Raviolifun/FiveBarRobot/CAD_Model/Electronics/motor-driver-odrive-v3-6-1.snapshot.2/motor driver.png

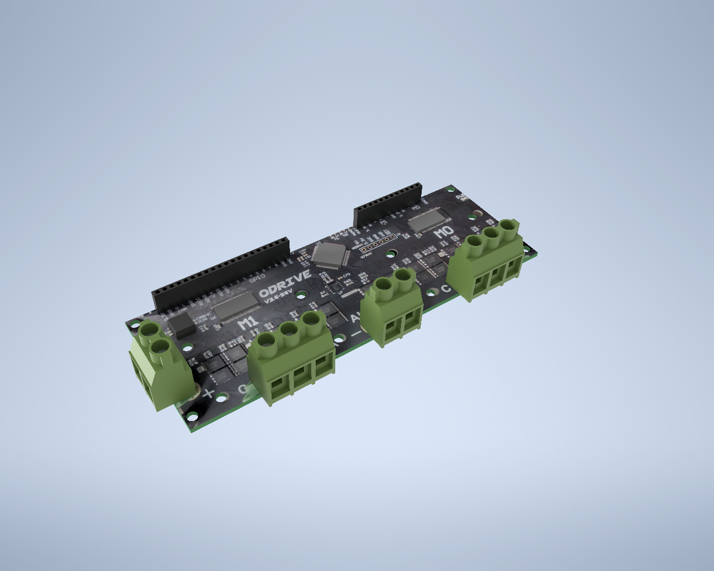
CAD_Model/Electronics/motor-driver-odrive-v3-6-1.snapshot.2/motor driver.png
