Raviolifun/FiveBarRobot/CAD_Model/Electronics/noctua-nf-a8-pwm-fan-80x80x25-1.snapshot.3/1.JPG

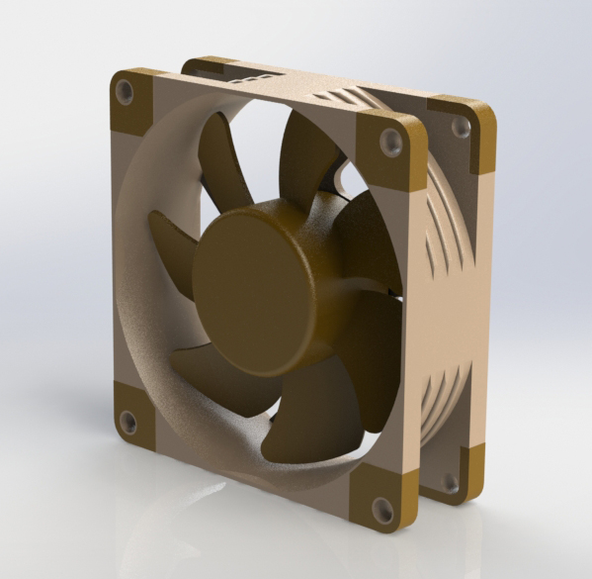
CAD_Model/Electronics/noctua-nf-a8-pwm-fan-80x80x25-1.snapshot.3/1.JPG
