Raviolifun/FiveBarRobot/CAD_Model/Motor/Renders/Motor1.JPG

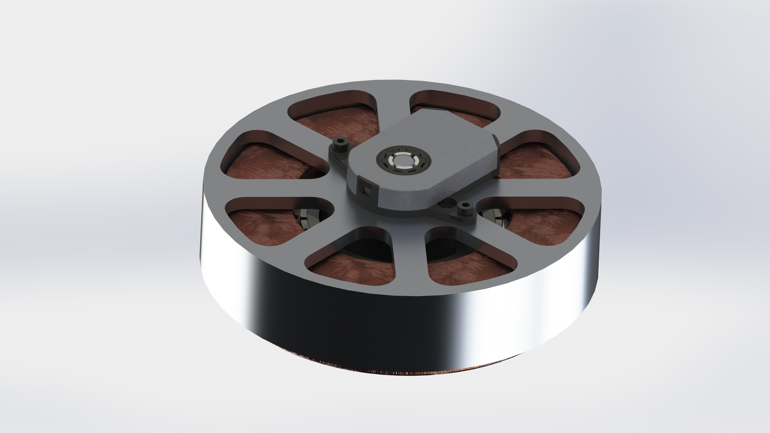
CAD_Model/Motor/Renders/Motor1.JPG
