Raviolifun/FiveBarRobot/CAD_Model/Renders/Robot.JPG

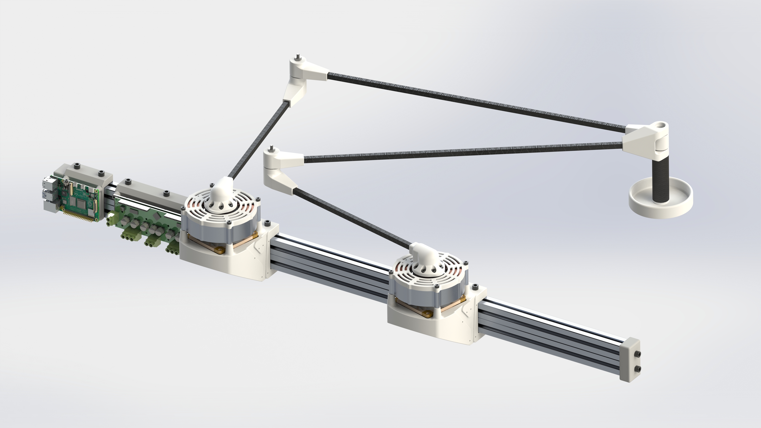
CAD_Model/Renders/Robot.JPG
