Raviolifun/FiveBarRobot/CAD_Model/Renders/Table.JPG

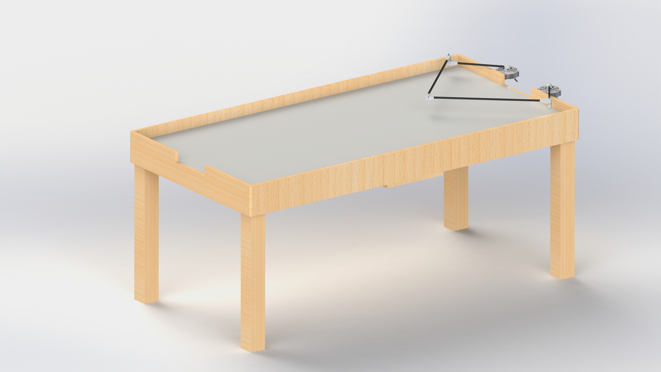
CAD_Model/Renders/Table.JPG
