Raviolifun/FiveBarRobot/CAD_Model/Renders/TableTop.JPG

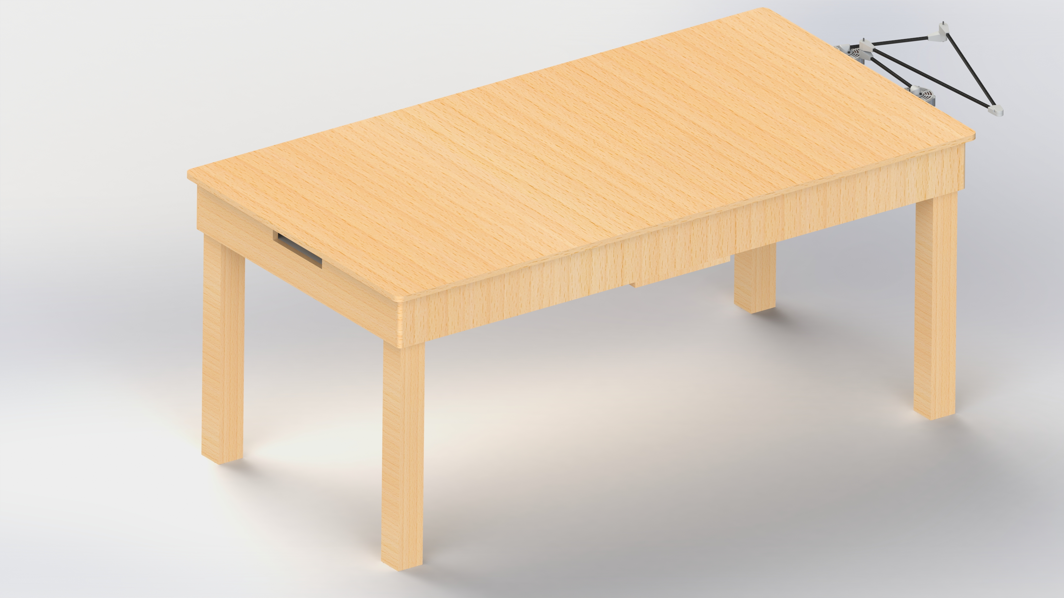
CAD_Model/Renders/TableTop.JPG
