Raviolifun/FiveBarRobot/Saves/animation.gif

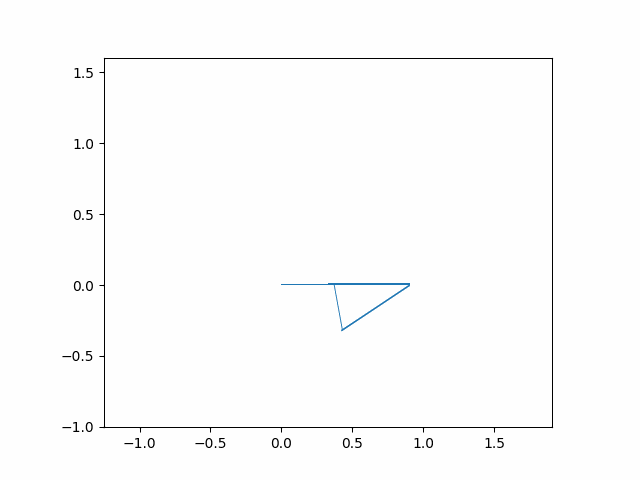
Saves/animation.gif
