Raviolifun/FiveBarRobot/Saves/e3.png

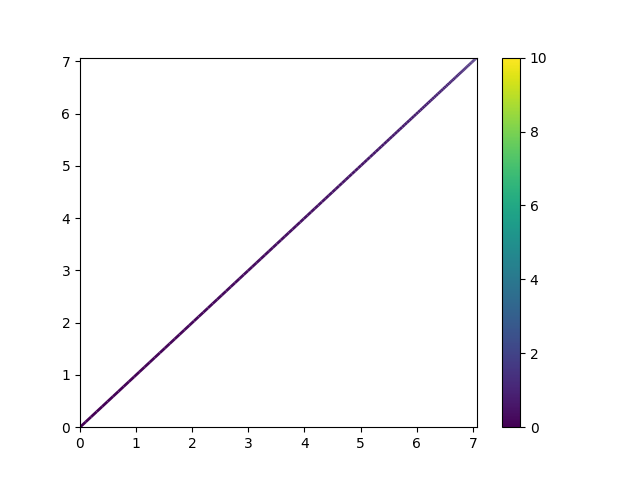
Saves/e3.png
