Raviolifun/FiveBarRobot/Saves/e3_hard.png

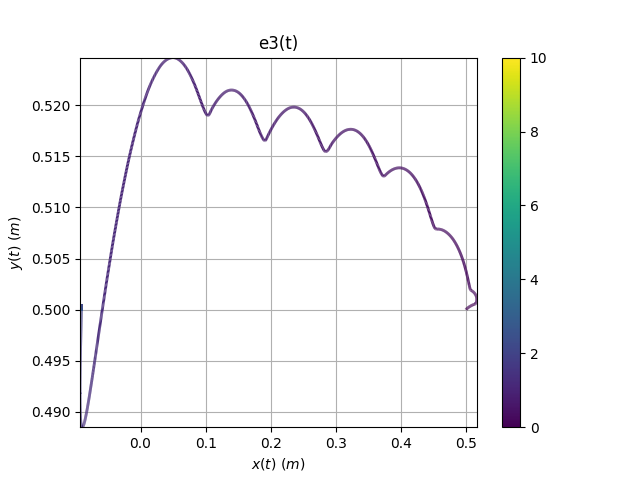
Saves/e3_hard.png
