Raviolifun/FiveBarRobot/Simulator/Saves/e3.png

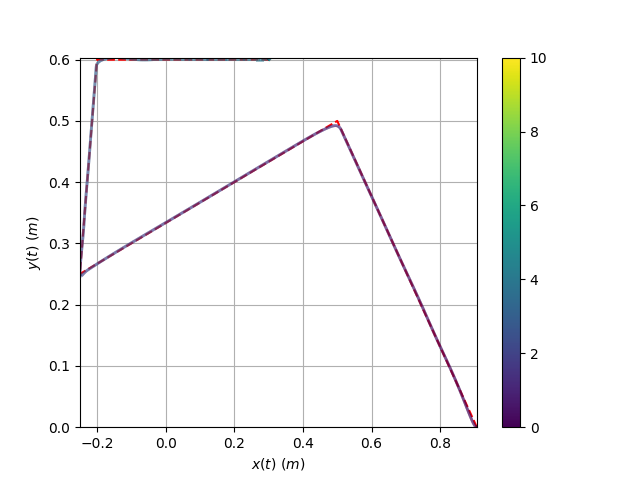
Simulator/Saves/e3.png
