Raviolifun/FiveBarRobot/Simulator/Visualize/Save/VisualizePlayArea.png

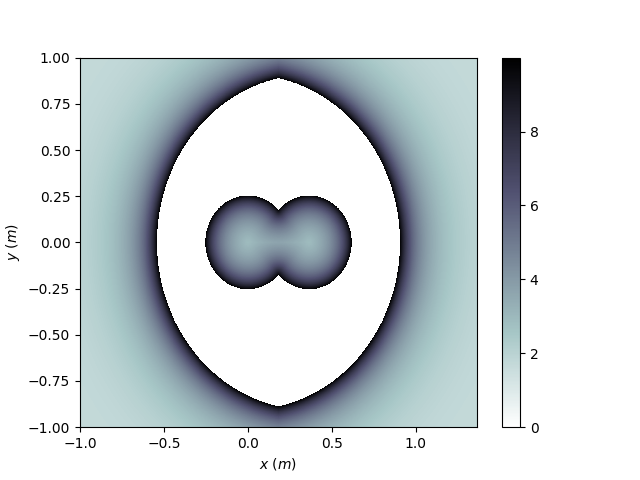
Simulator/Visualize/Save/VisualizePlayArea.png
