Raviolifun/FiveBarRobot/Simulator/Visualize/Save/VisualizePlayAreaDistance.png

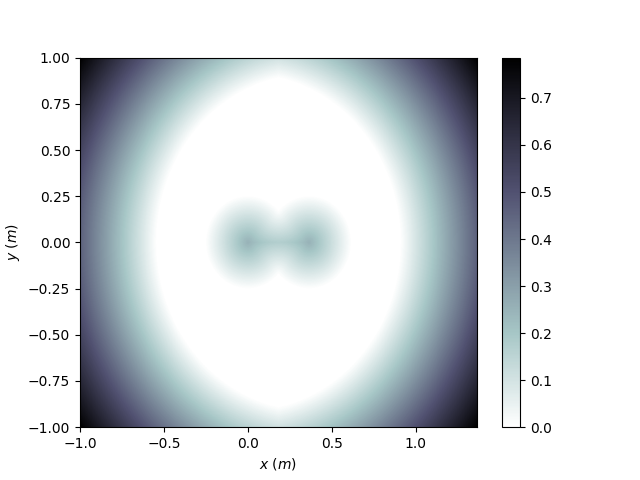
Simulator/Visualize/Save/VisualizePlayAreaDistance.png
