Raviolifun/FiveBarRobot/CAD_Model/Motor/Electronics/cui-devices-atm102-atm103-encoders-1.snapshot.5/FreeCAD Files/Encoders.FCStd

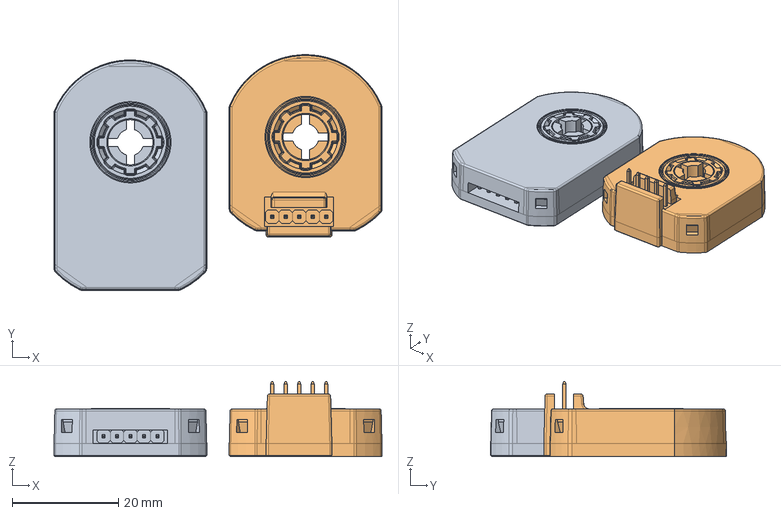
[picture p31: CAD file, 2023-01-07]
CAD_Model/Motor/Electronics/cui-devices-atm102-atm103-encoders-1.snapshot.5/FreeCAD Files/Encoders.FCStd
61.8 x 44.4 x 14.2 mm
ATM102 Encoder_001
ATM103 Encoder_001
