Raviolifun/FiveBarRobot/CAD_Model/Motor/StatorRotor/RI100-210120.stp

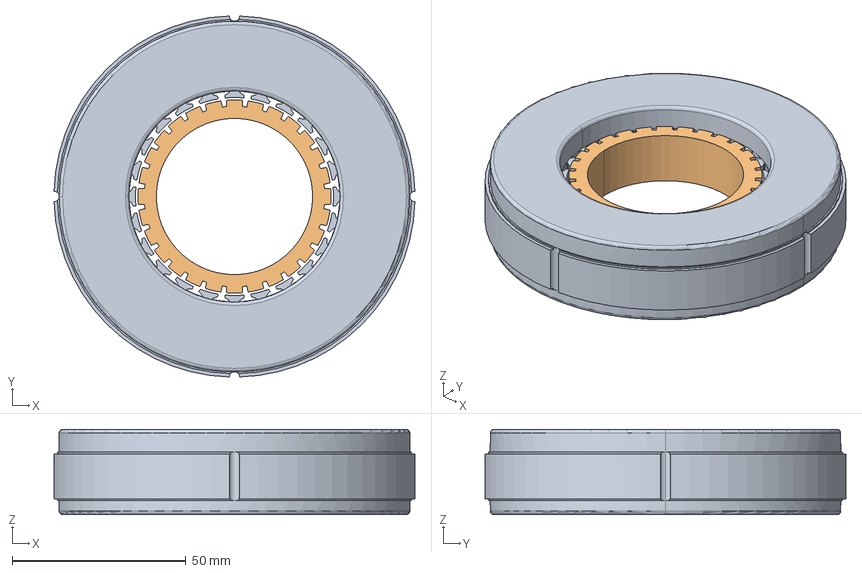
[picture p32: CAD file, 2022-10-18]
CAD_Model/Motor/StatorRotor/RI100-210120.stp
104.0 x 104.0 x 24.5 mm
