Raviolifun/FiveBarRobot/CAD_Model/TestSystem/TestSystem_1.STL

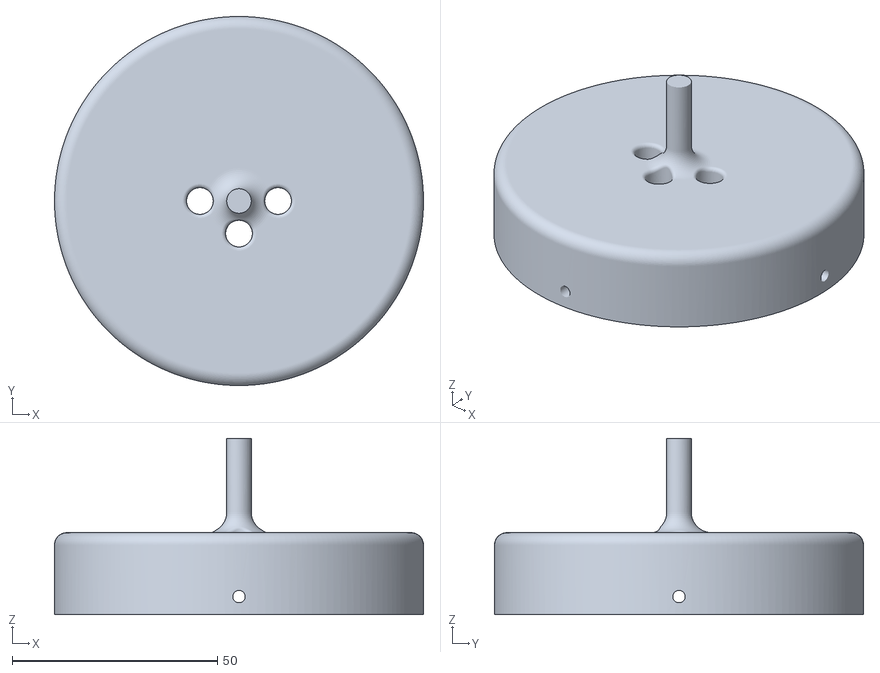
[picture p33: CAD file, 2023-04-11]
CAD_Model/TestSystem/TestSystem_1.STL
90.0 x 90.0 x 43.0
