Raviolifun/FiveBarRobot/CAM_Profiles/2x_StatorWorkHolding.STL

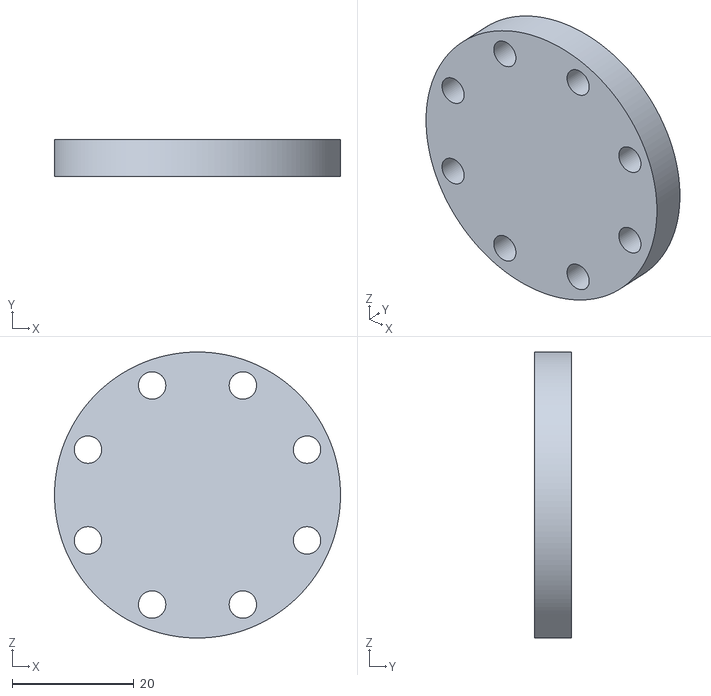
[picture p34: CAD file, 2023-04-11]
CAM_Profiles/2x_StatorWorkHolding.STL
47.0 x 6.00 x 47.0
