Raviolifun/FiveBarRobot/CAD_Model/AirTable/Electronics Mount.SLDPRT

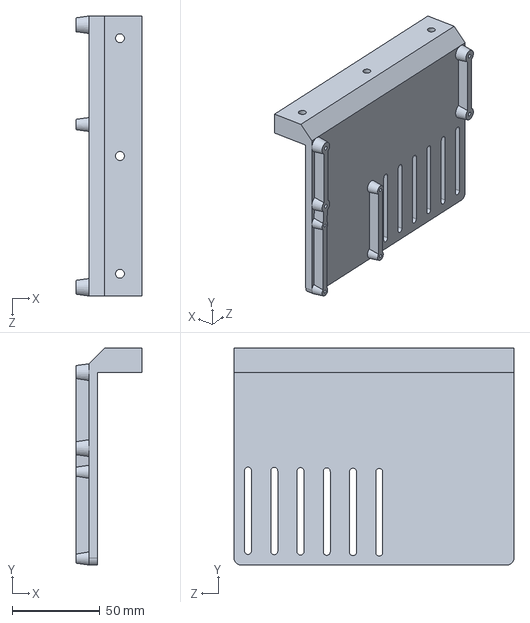
[picture p35: CAD file, 2023-02-09]
CAD_Model/AirTable/Electronics Mount.SLDPRT
37.9 x 124.0 x 160.0 mm
