Raviolifun/FiveBarRobot/CAD_Model/AirTable/SubParts/Leg2.SLDPRT

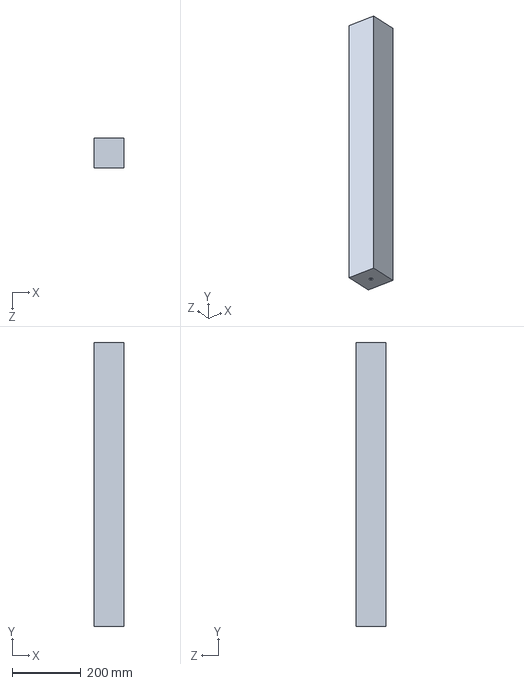
[picture p36: CAD file, 2023-02-06]
CAD_Model/AirTable/SubParts/Leg2.SLDPRT
88.9 x 828.7 x 88.9 mm
