Raviolifun/FiveBarRobot/CAD_Model/Electronics/noctua-nf-a8-pwm-fan-80x80x25-1.snapshot.3/Import_Noctua nf-a8-pwm fan 80x80x25.SLDPRT

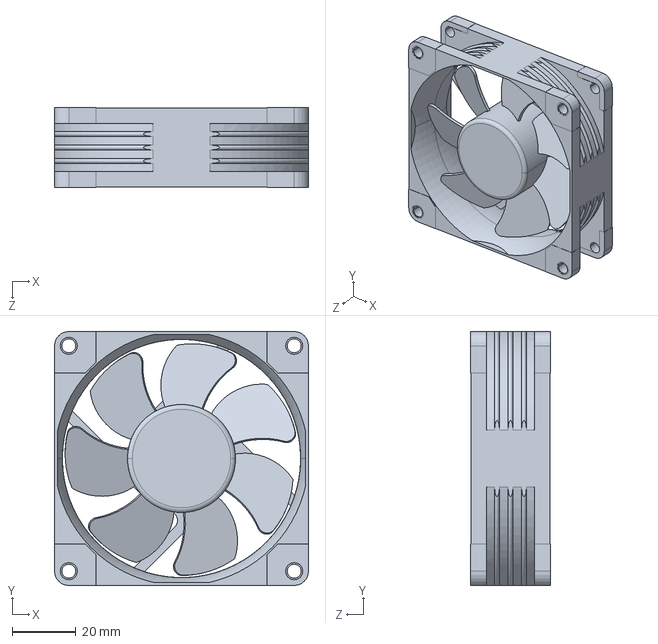
[picture p37: CAD file, 2023-02-09]
CAD_Model/Electronics/noctua-nf-a8-pwm-fan-80x80x25-1.snapshot.3/Import_Noctua nf-a8-pwm fan 80x80x25.SLDPRT
80.0 x 80.0 x 25.2 mm
