Raviolifun/FiveBarRobot/CAD_Model/Electronics/raspberry-pi-4-model-b-1.snapshot.3/2.54 mm DUPONT MALE PIN HEADER, IO, 2X20, RPi4ModelB.SLDPRT

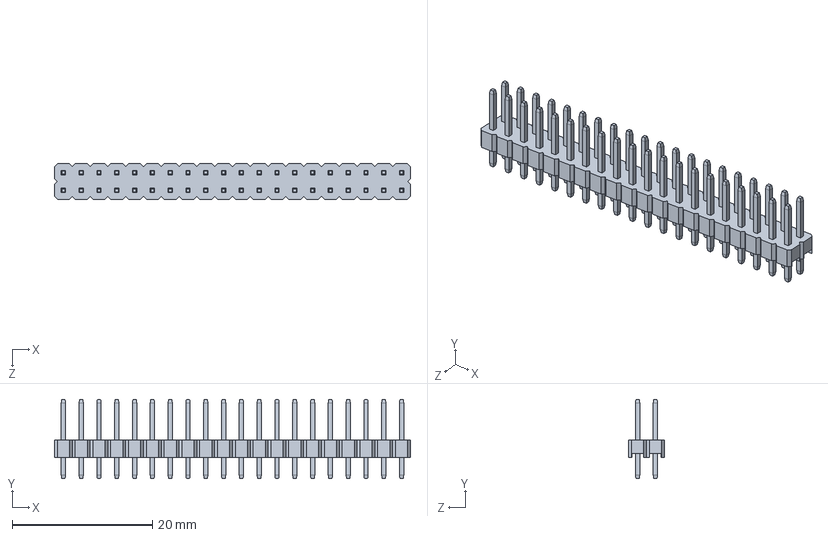
[picture p38: CAD file, 2023-01-13]
CAD_Model/Electronics/raspberry-pi-4-model-b-1.snapshot.3/2.54 mm DUPONT MALE PIN HEADER, IO, 2X20, RPi4ModelB.SLDPRT
50.8 x 11.3 x 5.08 mm
