Raviolifun/FiveBarRobot/CAD_Model/Export3DPrinting/Robot_EndJoint_Spacer.STL

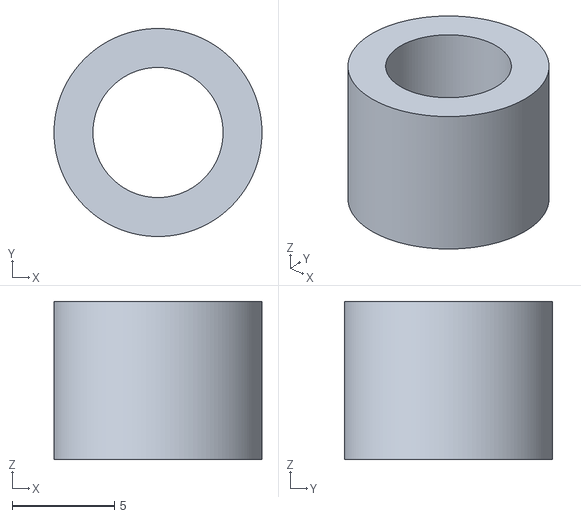
[picture p39: CAD file, 2023-04-05]
CAD_Model/Export3DPrinting/Robot_EndJoint_Spacer.STL
10.2 x 10.2 x 7.72
