Raviolifun/FiveBarRobot/CAD_Model/Export3DPrinting/ToPrint/Aestetic_Edge_Guard.STL

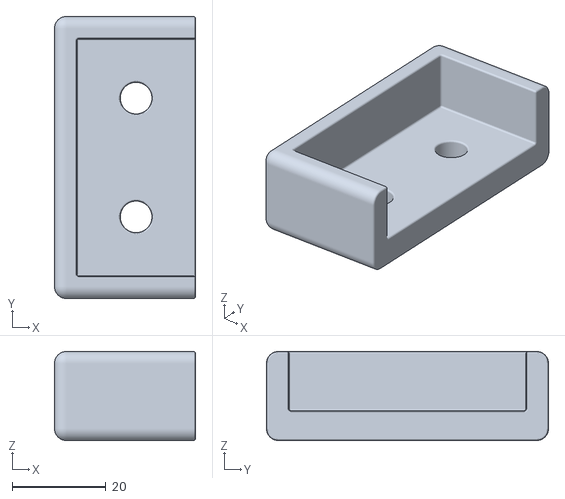
[picture p40: CAD file, 2023-02-09]
CAD_Model/Export3DPrinting/ToPrint/Aestetic_Edge_Guard.STL
30.2 x 60.3 x 19.1
