Raviolifun/FiveBarRobot/CAD_Model/Motor/Electronics/cui-devices-atm102-atm103-encoders-1.snapshot.5/ATM103 Encoder.step

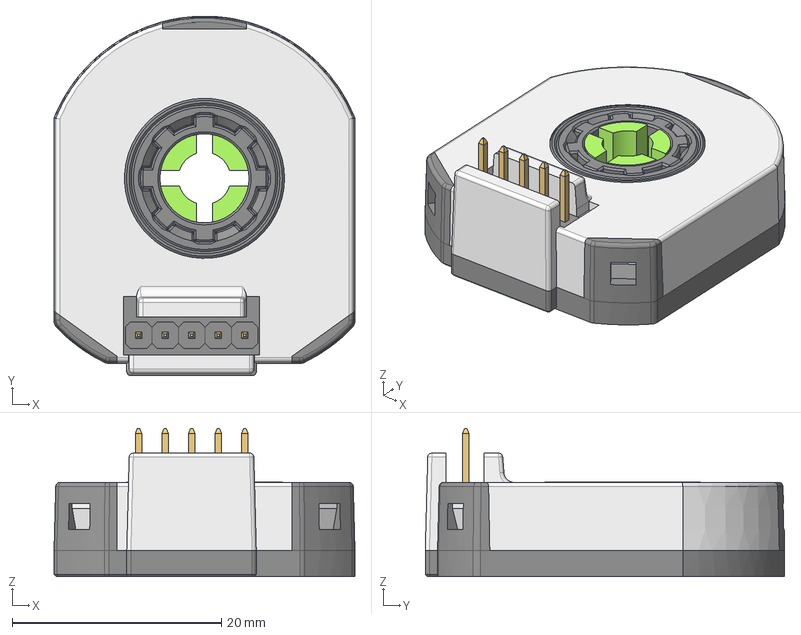
[picture p41: CAD file, 2023-01-07]
CAD_Model/Motor/Electronics/cui-devices-atm102-atm103-encoders-1.snapshot.5/ATM103 Encoder.step
28.8 x 34.4 x 14.2 mm
