Raviolifun/FiveBarRobot/CAD_Model/Motor/Stator.SLDPRT

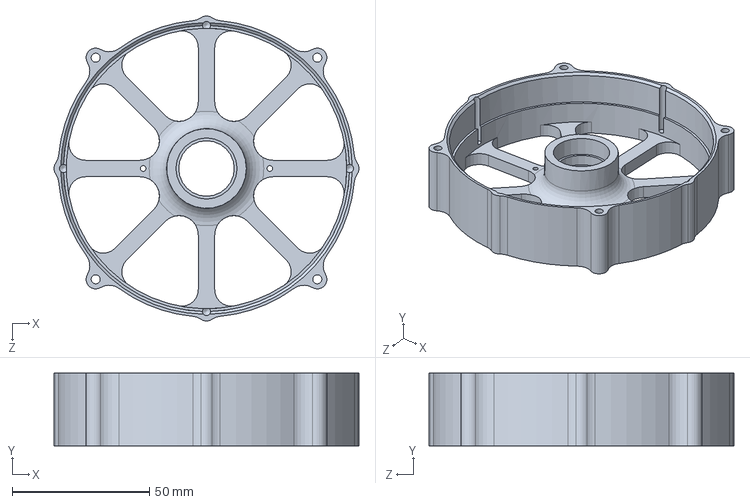
[picture p42: CAD file, 2023-02-06]
CAD_Model/Motor/Stator.SLDPRT
110.9 x 26.5 x 110.9 mm
