Raviolifun/FiveBarRobot/CAD_Model/TestSystem/TestSystem_2.STL

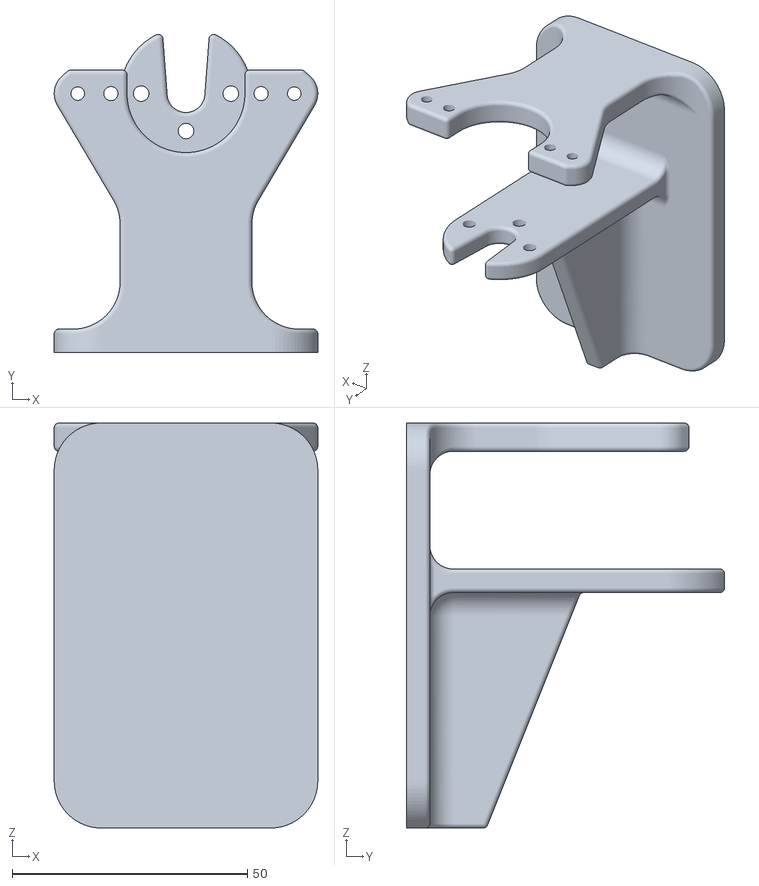
[picture p43: CAD file, 2023-04-11]
CAD_Model/TestSystem/TestSystem_2.STL
56.0 x 67.6 x 86.0
