Raviolifun/FiveBarRobot/CAM_Profiles/StatorWorkHolding.STEP

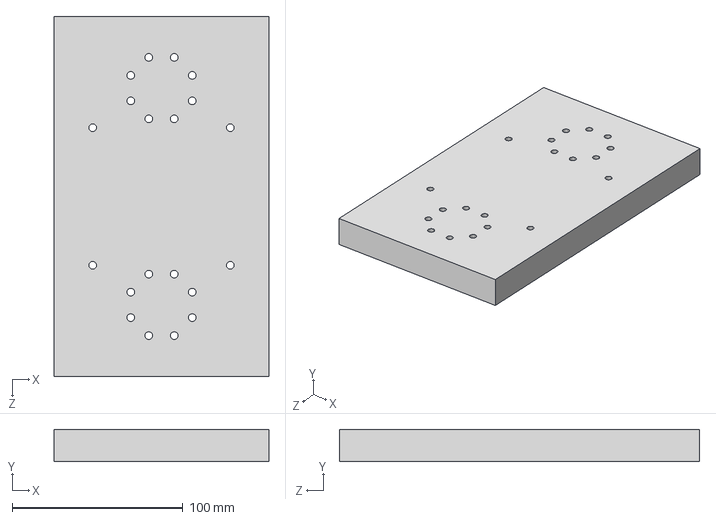
[picture p44: CAD file, 2023-04-11]
CAM_Profiles/StatorWorkHolding.STEP
126.0 x 19.0 x 211.1 mm
