Raviolifun/FiveBarRobot/CAD_Model/AirTable/SubParts/DuctBottom.SLDPRT

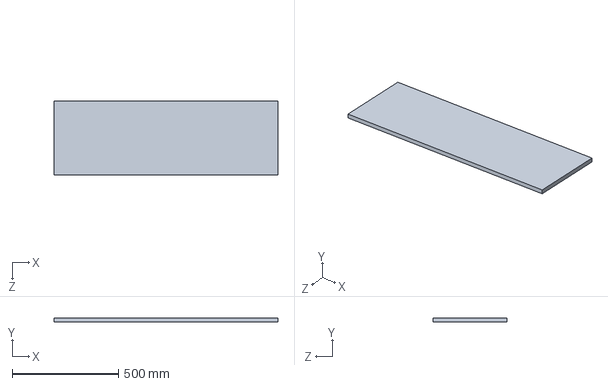
[picture p45: CAD file, 2023-02-06]
CAD_Model/AirTable/SubParts/DuctBottom.SLDPRT
1054.1 x 19.1 x 346.1 mm
