Raviolifun/FiveBarRobot/CAD_Model/Electronics/raspberry-pi-4-model-b-1.snapshot.3/91D77 D9WHV 778K, 4 GB LPDDR4 SDRAM, RPi4ModelB.SLDPRT

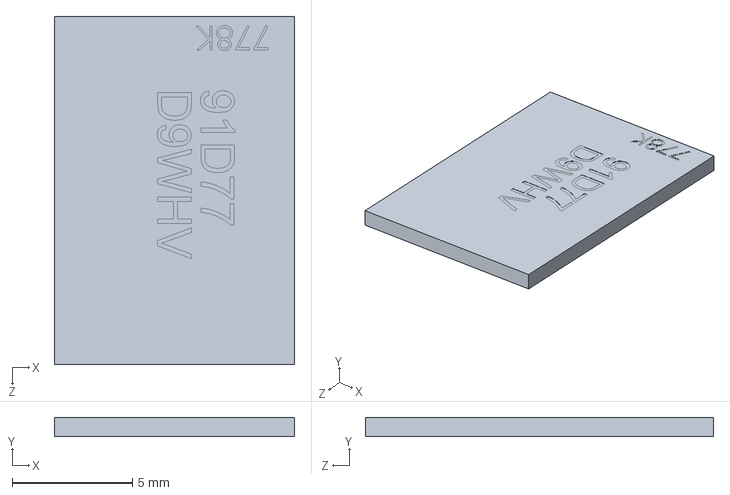
[picture p46: CAD file, 2023-01-13]
CAD_Model/Electronics/raspberry-pi-4-model-b-1.snapshot.3/91D77 D9WHV 778K, 4 GB LPDDR4 SDRAM, RPi4ModelB.SLDPRT
10.0 x 0.8 x 14.5 mm
