Raviolifun/FiveBarRobot/CAD_Model/Motor/Rotor.SLDPRT

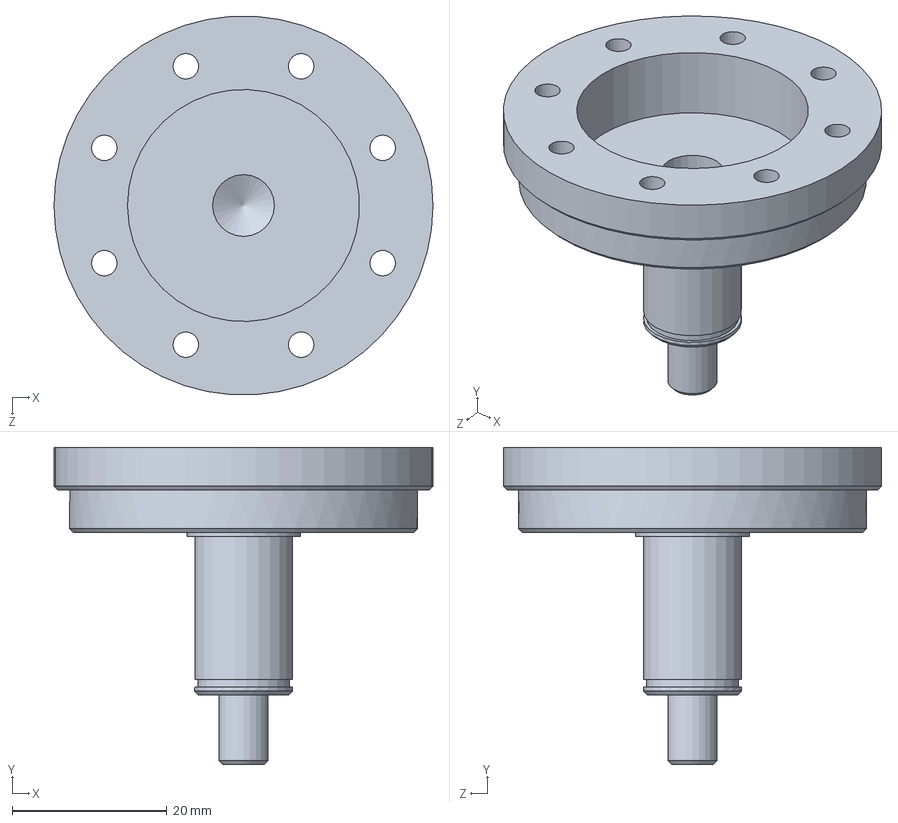
[picture p47: CAD file, 2023-02-06]
CAD_Model/Motor/Rotor.SLDPRT
49.0 x 41.0 x 48.9 mm
