Raviolifun/FiveBarRobot/CAD_Model/TestSystem/TestSystem.SLDPRT

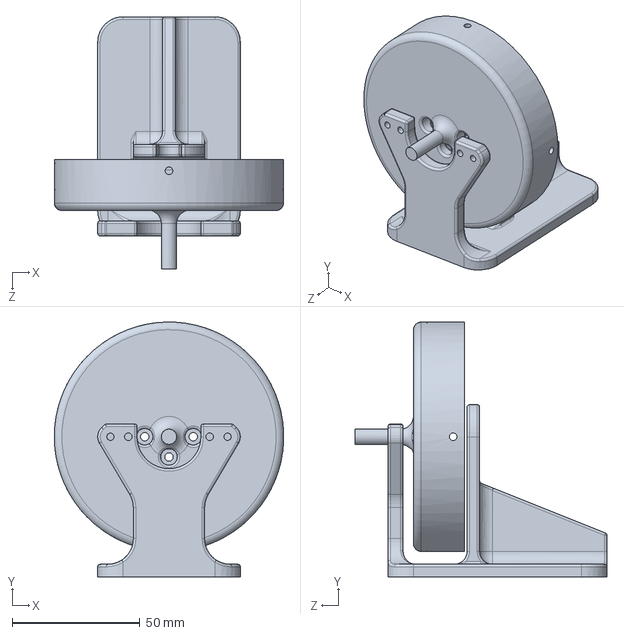
[picture p48: CAD file, 2023-04-11]
CAD_Model/TestSystem/TestSystem.SLDPRT
90.0 x 100.0 x 99.0 mm
