Raviolifun/FiveBarRobot/CAM_Profiles/Rotor.STEP

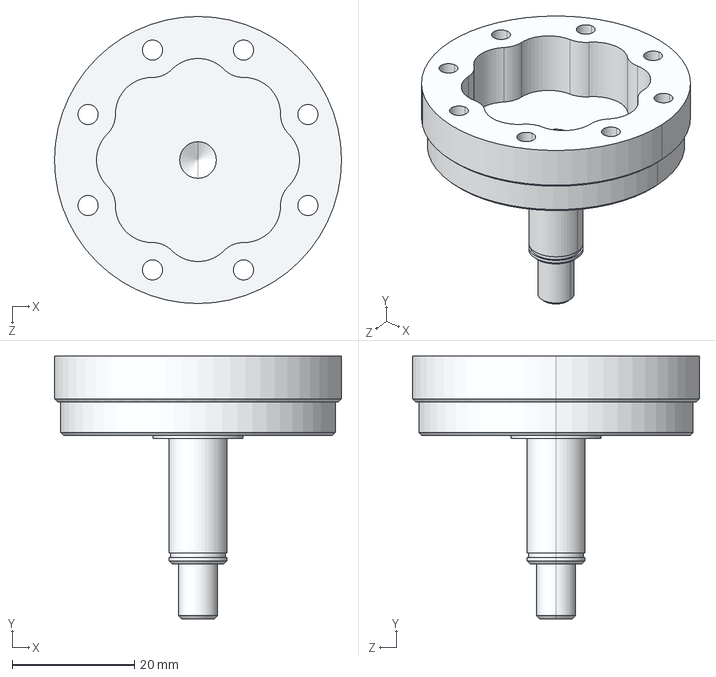
[picture p49: CAD file, 2023-04-05]
CAM_Profiles/Rotor.STEP
47.0 x 43.0 x 47.0 mm
