Raviolifun/FiveBarRobot/CAD_Model/AirTable/Motor Controller Mount.SLDPRT

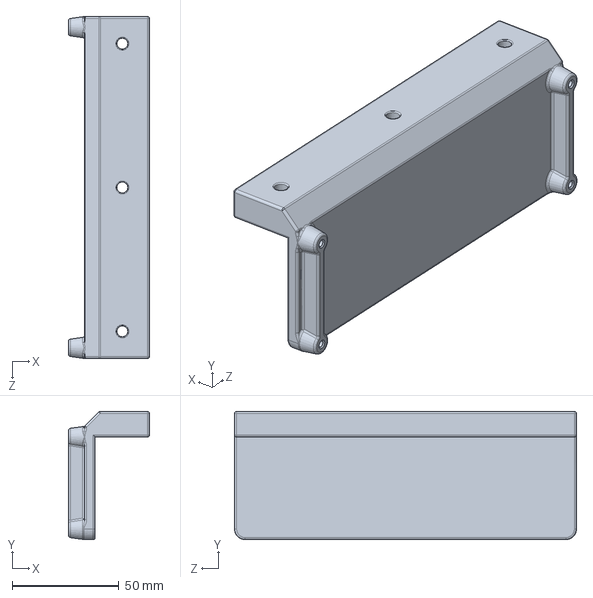
[picture p50: CAD file, 2023-02-09]
CAD_Model/AirTable/Motor Controller Mount.SLDPRT
37.9 x 60.0 x 160.0 mm
