Raviolifun/FiveBarRobot/CAD_Model/AirTable/SubParts/Corner Locator3.SLDPRT

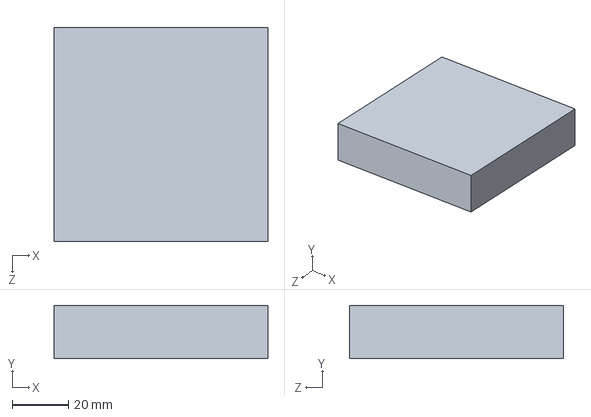
[picture p51: CAD file, 2023-02-06]
CAD_Model/AirTable/SubParts/Corner Locator3.SLDPRT
76.2 x 19.1 x 76.2 mm
