Raviolifun/FiveBarRobot/CAD_Model/Electronics/raspberry-pi-4-model-b-1.snapshot.3/Broadcom BCM54213PE Gigabit Ethernet Transceiver, RPi4ModelB.SLDPRT

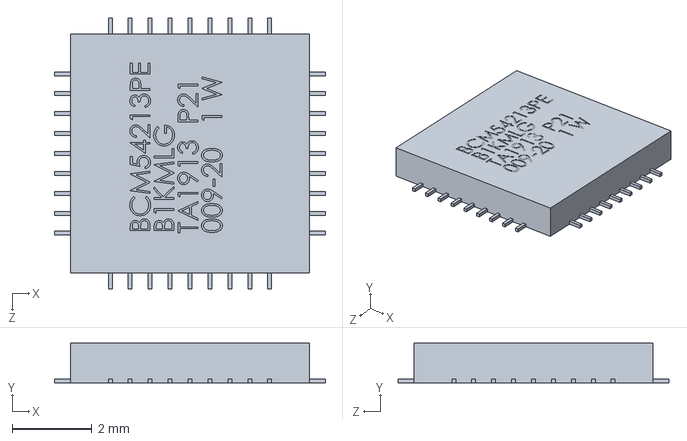
[picture p52: CAD file, 2023-01-13]
CAD_Model/Electronics/raspberry-pi-4-model-b-1.snapshot.3/Broadcom BCM54213PE Gigabit Ethernet Transceiver, RPi4ModelB.SLDPRT
6.80 x 1.00 x 6.80 mm
