Raviolifun/FiveBarRobot/CAD_Model/Export3DPrinting/Robot_Elbow2V2.STL

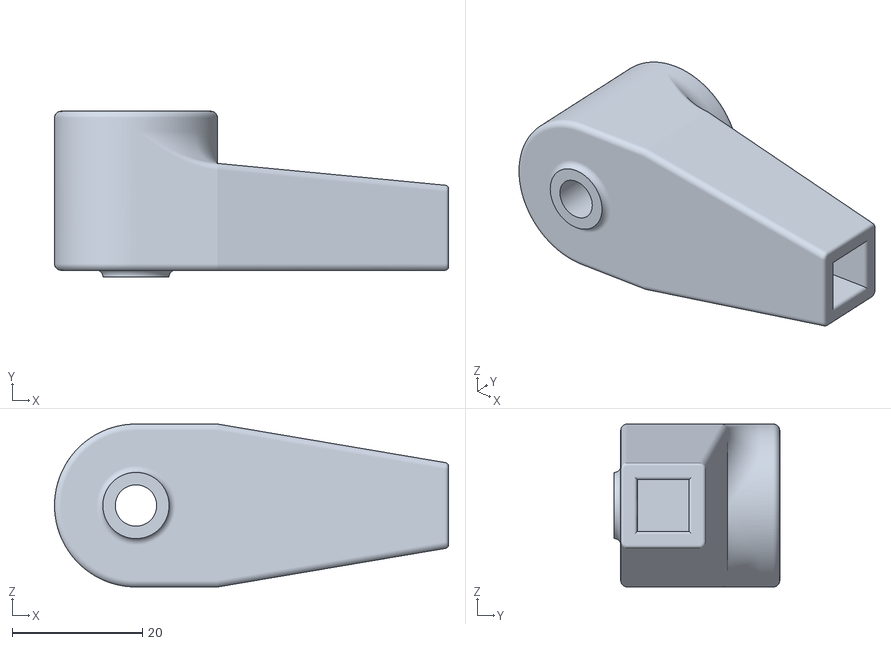
[picture p53: CAD file, 2023-02-09]
CAD_Model/Export3DPrinting/Robot_Elbow2V2.STL
60.4 x 25.4 x 25.0
