Raviolifun/FiveBarRobot/CAD_Model/Linkage/Elbow1V2.SLDPRT

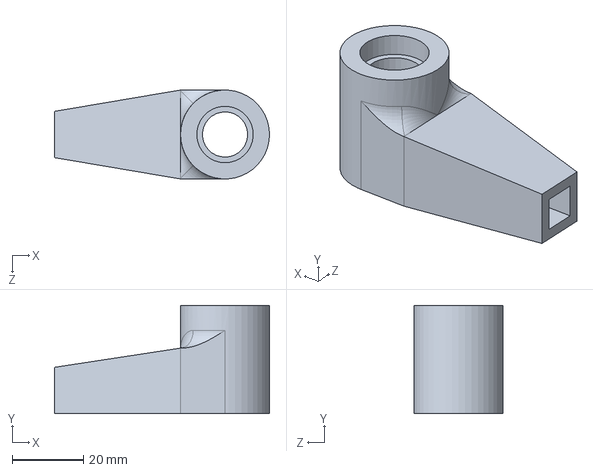
[picture p54: CAD file, 2023-04-20]
CAD_Model/Linkage/Elbow1V2.SLDPRT
60.4 x 30.4 x 25.0 mm
