Raviolifun/FiveBarRobot/CAD_Model/Linkage/OTS/6455K8_Plastic Ball Bearing.SLDPRT

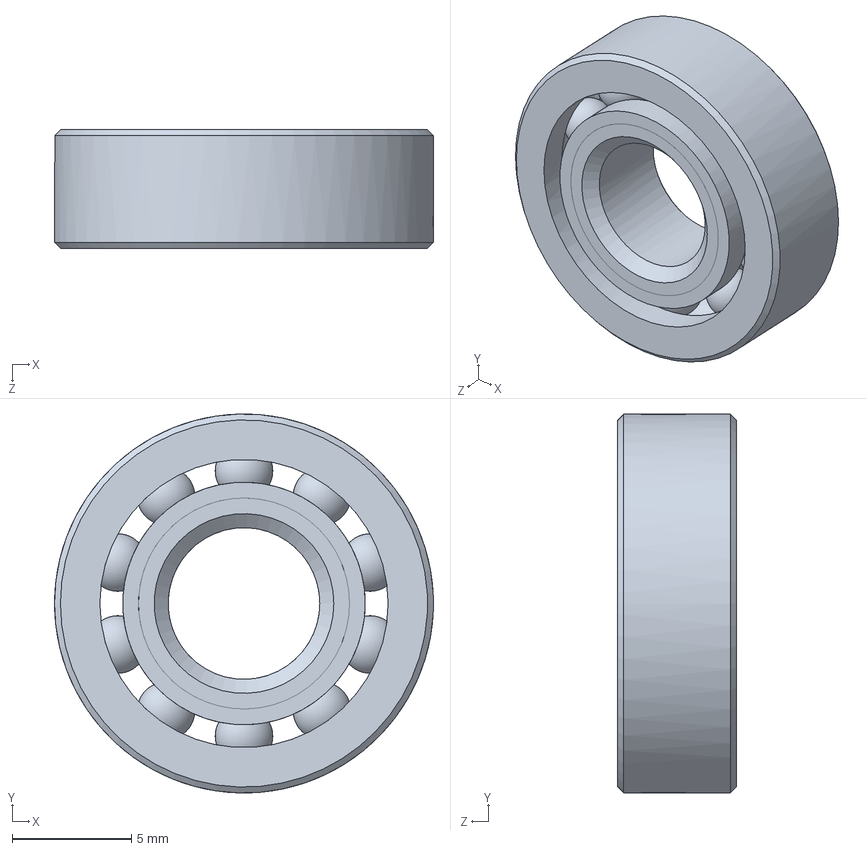
[picture p55: CAD file, 2023-02-06]
CAD_Model/Linkage/OTS/6455K8_Plastic Ball Bearing.SLDPRT
15.9 x 15.9 x 4.98 mm
