Raviolifun/FiveBarRobot/CAD_Model/Motor/RotorShaft.SLDPRT

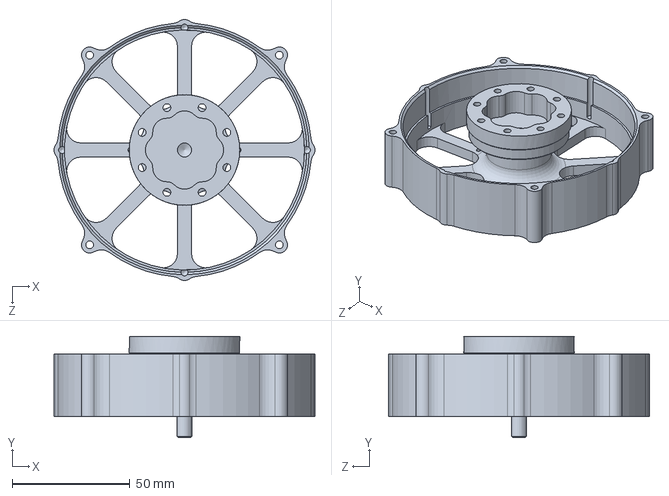
[picture p56: CAD file, 2023-02-06]
CAD_Model/Motor/RotorShaft.SLDPRT
110.9 x 43.0 x 110.9 mm
