Raviolifun/FiveBarRobot/CAM_Profiles/Stator.STEP

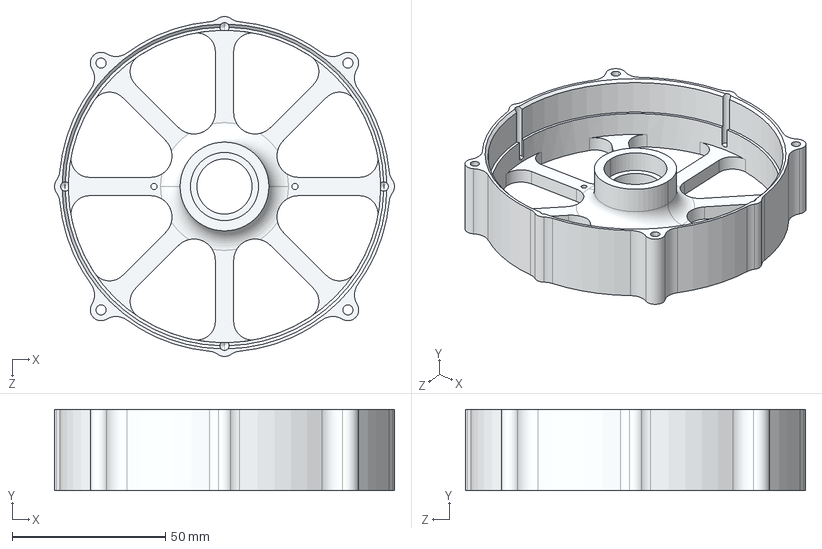
[picture p57: CAD file, 2023-04-05]
CAM_Profiles/Stator.STEP
111.0 x 26.5 x 111.0 mm
