Raviolifun/FiveBarRobot/CAD_Model/AirTable/Mounting for Motors.SLDPRT

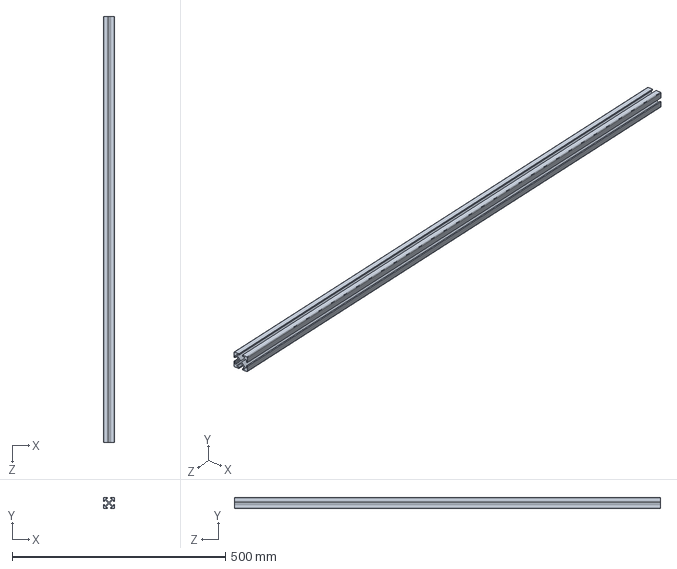
[picture p58: CAD file, 2023-02-09]
CAD_Model/AirTable/Mounting for Motors.SLDPRT
25.4 x 25.4 x 1000.0 mm
