Raviolifun/FiveBarRobot/CAD_Model/AirTable/SubParts/Top.SLDPRT

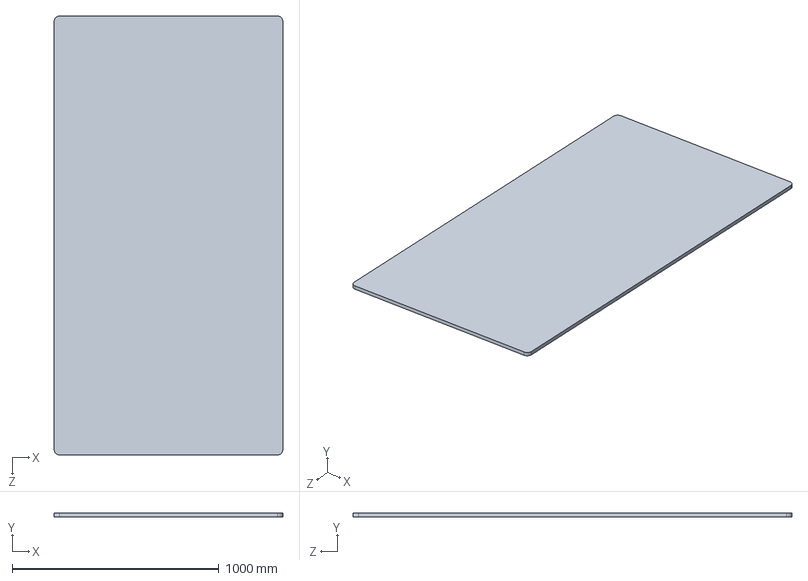
[picture p59: CAD file, 2023-02-06]
CAD_Model/AirTable/SubParts/Top.SLDPRT
1104.9 x 19.1 x 2120.9 mm
