Raviolifun/FiveBarRobot/CAD_Model/Export3DPrinting/Robot_Outisde_Hand.STL

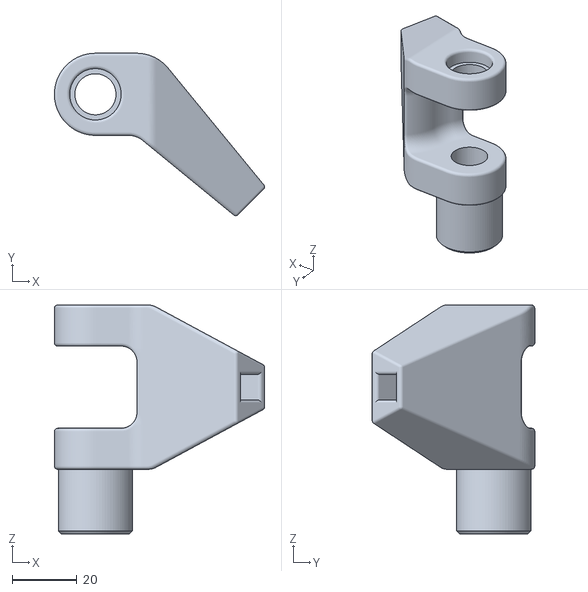
[picture p61: CAD file, 2023-02-09]
CAD_Model/Export3DPrinting/Robot_Outisde_Hand.STL
65.0 x 50.3 x 70.8
