Raviolifun/FiveBarRobot/CAD_Model/Motor/Cover.SLDPRT

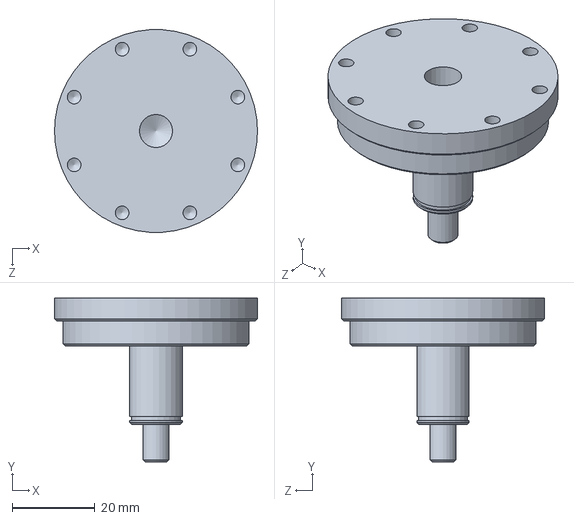
[picture p62: CAD file, 2023-01-07]
CAD_Model/Motor/Cover.SLDPRT
49.0 x 39.5 x 48.9 mm
