Raviolifun/FiveBarRobot/CAD_Model/AirTable/MotorMount.SLDPRT

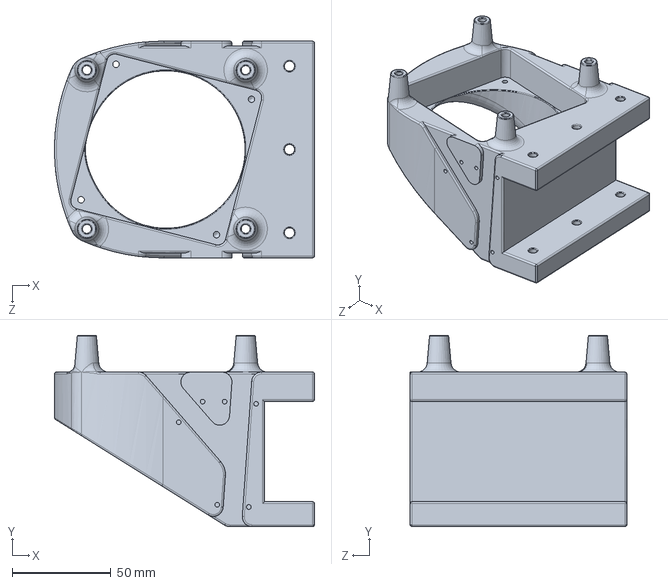
[picture p63: CAD file, 2023-02-09]
CAD_Model/AirTable/MotorMount.SLDPRT
132.0 x 97.2 x 110.0 mm
