Raviolifun/FiveBarRobot/CAD_Model/AirTable/SubParts/Front1.SLDPRT

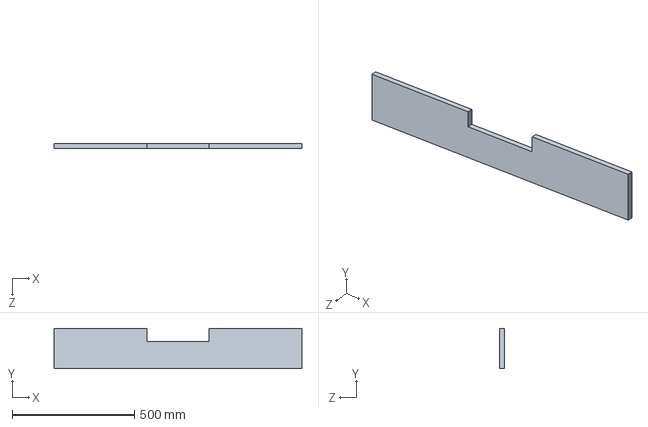
[picture p64: CAD file, 2023-02-06]
CAD_Model/AirTable/SubParts/Front1.SLDPRT
1016.0 x 165.1 x 19.1 mm
