Raviolifun/FiveBarRobot/CAD_Model/Electronics/raspberry-pi-4-model-b-1.snapshot.3/Female Micro HDMI Connector, RPi4ModelB.SLDPRT

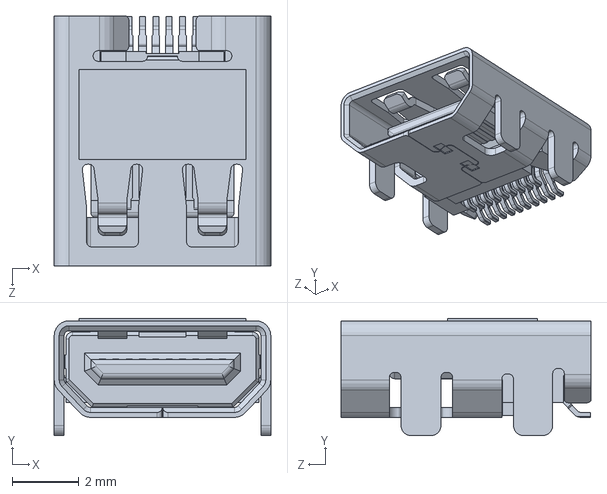
[picture p65: CAD file, 2023-01-13]
CAD_Model/Electronics/raspberry-pi-4-model-b-1.snapshot.3/Female Micro HDMI Connector, RPi4ModelB.SLDPRT
6.50 x 3.52 x 7.50 mm
