Raviolifun/FiveBarRobot/CAD_Model/Export3DPrinting/Robot_Elbow1V2.STL

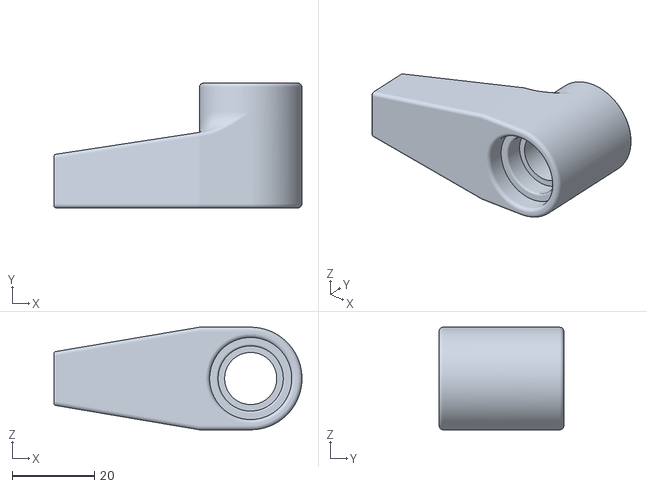
[picture p66: CAD file, 2023-02-09]
CAD_Model/Export3DPrinting/Robot_Elbow1V2.STL
60.4 x 30.4 x 25.0
