Raviolifun/FiveBarRobot/CAD_Model/Linkage/Inside_Hand.SLDPRT

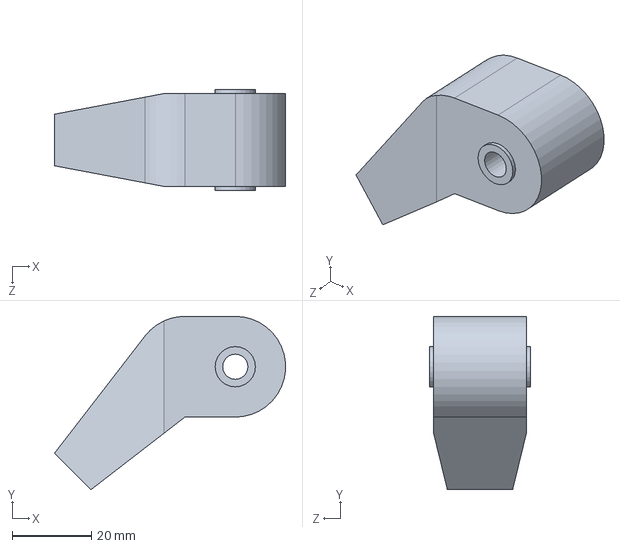
[picture p67: CAD file, 2023-04-05]
CAD_Model/Linkage/Inside_Hand.SLDPRT
58.2 x 43.7 x 25.4 mm
