Raviolifun/FiveBarRobot/CAD_Model/AirTable/Air Table.SLDPRT

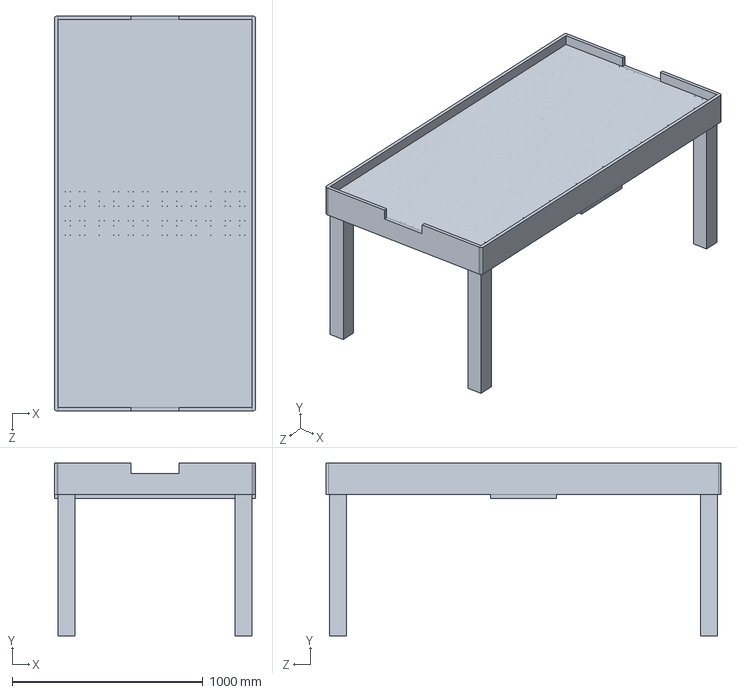
[picture p68: CAD file, 2023-01-26]
CAD_Model/AirTable/Air Table.SLDPRT
1054.1 x 904.9 x 2070.1 mm
