Raviolifun/FiveBarRobot/CAD_Model/Electronics/raspberry-pi-4-model-b-1.snapshot.3/Camera Connector, RPi4ModelB.SLDPRT

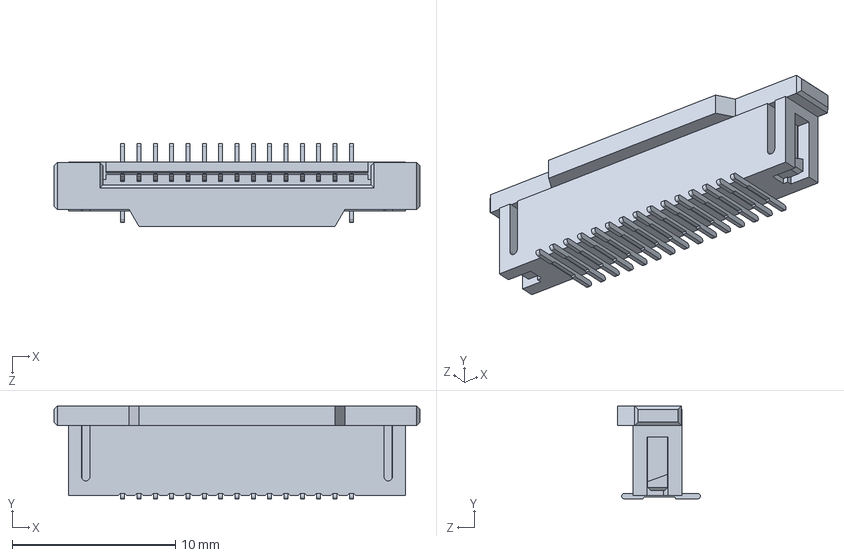
[picture p69: CAD file, 2023-01-13]
CAD_Model/Electronics/raspberry-pi-4-model-b-1.snapshot.3/Camera Connector, RPi4ModelB.SLDPRT
22.4 x 5.68 x 5.07 mm
