Raviolifun/FiveBarRobot/CAD_Model/Linkage/Mallet.SLDPRT

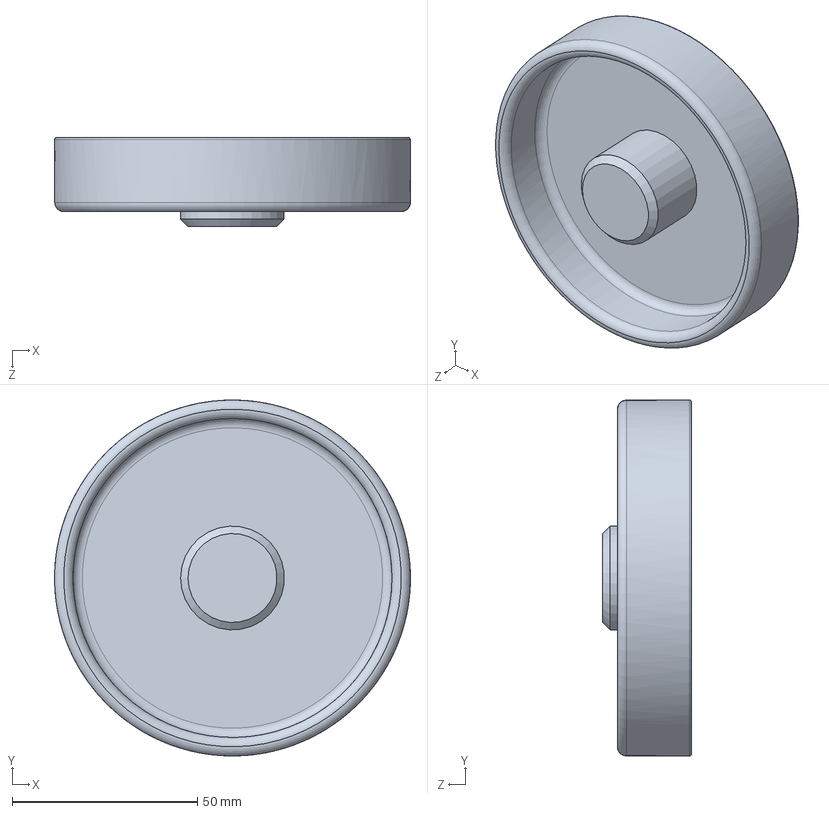
[picture p71: CAD file, 2023-04-05]
CAD_Model/Linkage/Mallet.SLDPRT
96.0 x 96.0 x 24.0 mm
