Raviolifun/FiveBarRobot/CAD_Model/AirTable/Ducts.STEP

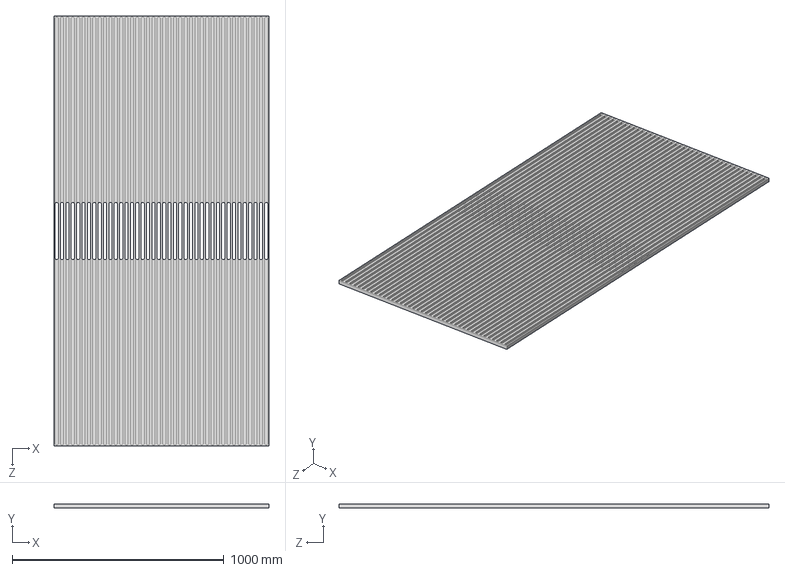
[picture p72: CAD file, 2023-01-13]
CAD_Model/AirTable/Ducts.STEP
1016.0 x 19.1 x 2032.0 mm
