Raviolifun/FiveBarRobot/CAD_Model/Electronics/raspberry-pi-4-model-b-1.snapshot.3/2X USB3.0 PORTS, RPi4ModelB.SLDPRT

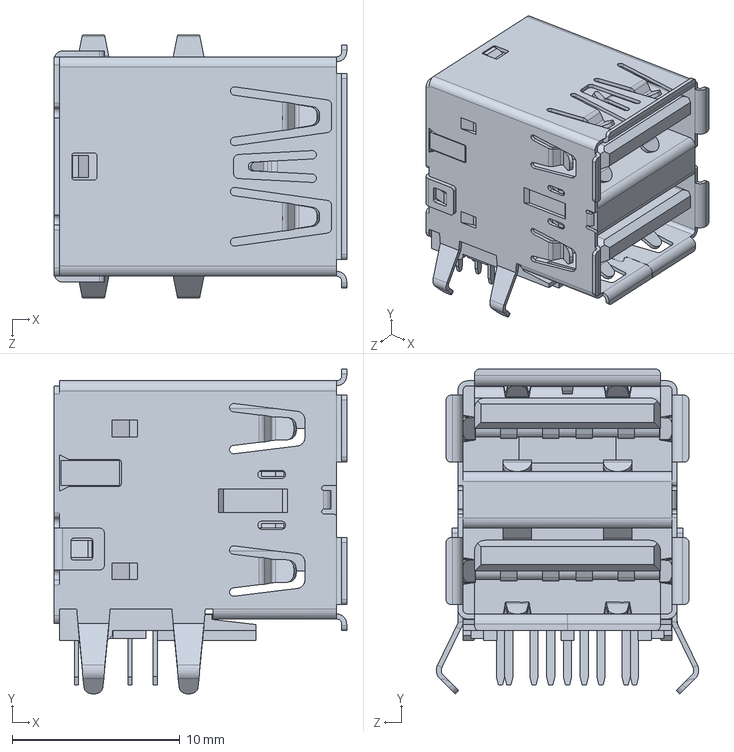
[picture p73: CAD file, 2023-01-13]
CAD_Model/Electronics/raspberry-pi-4-model-b-1.snapshot.3/2X USB3.0 PORTS, RPi4ModelB.SLDPRT
17.5 x 19.4 x 15.7 mm
