Raviolifun/FiveBarRobot/CAD_Model/Linkage/Outisde_Hand.SLDPRT

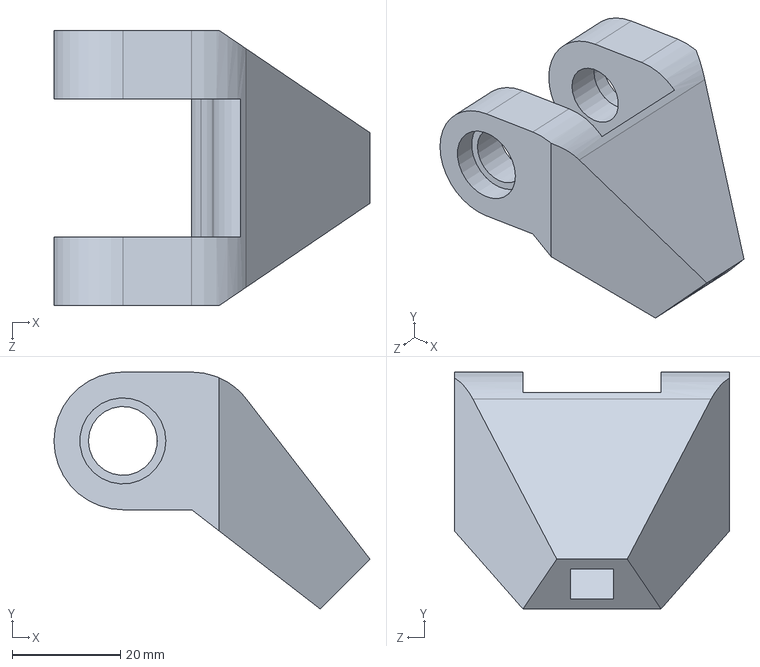
[picture p74: CAD file, 2023-04-05]
CAD_Model/Linkage/Outisde_Hand.SLDPRT
58.3 x 43.7 x 50.8 mm
