Raviolifun/FiveBarRobot/CAD_Model/Motor/OTS/0.500 ID x 0.875 OD x 0.281 WD (Radial Bearing) (217-3337).step

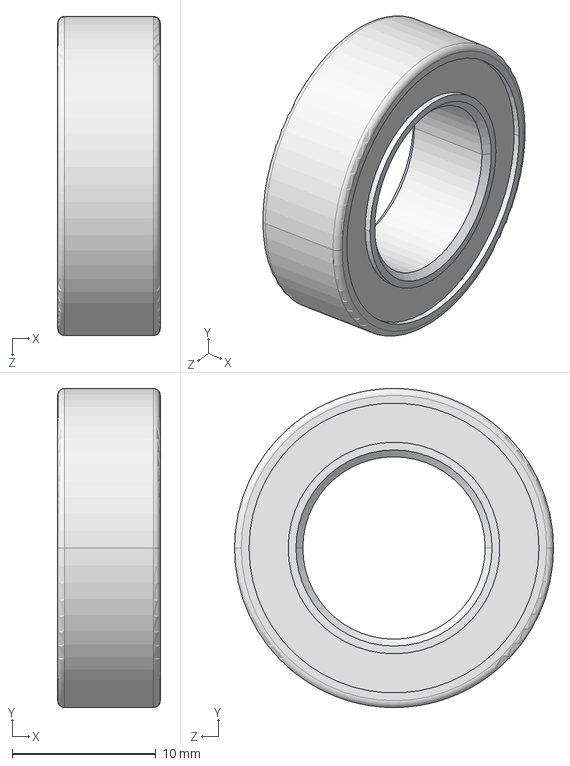
[picture p75: CAD file, 2023-01-07]
CAD_Model/Motor/OTS/0.500 ID x 0.875 OD x 0.281 WD (Radial Bearing) (217-3337).step
7.14 x 22.2 x 22.2 mm
