Raviolifun/FiveBarRobot/CAD_Model/AirTable/Puck.SLDPRT

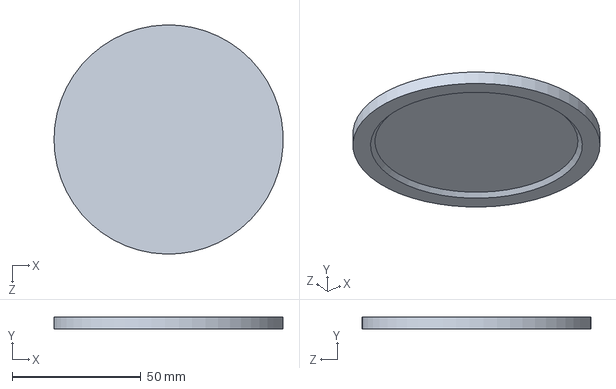
[picture p76: CAD file, 2023-01-13]
CAD_Model/AirTable/Puck.SLDPRT
88.8 x 4.76 x 88.9 mm
