Raviolifun/FiveBarRobot/CAD_Model/Export3DPrinting/Robot_Mallet.STL

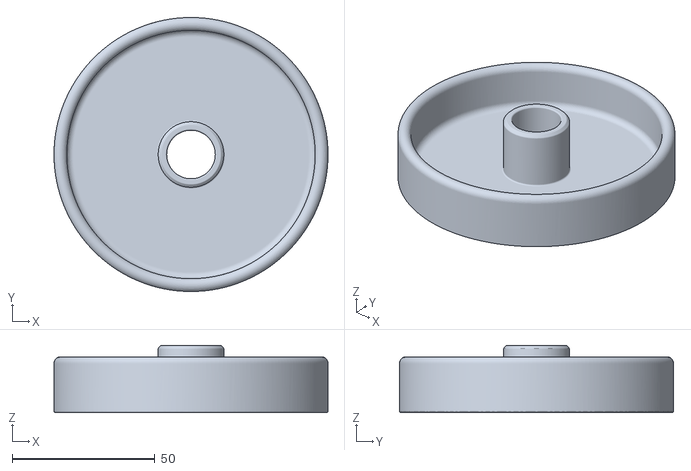
[picture p77: CAD file, 2023-02-09]
CAD_Model/Export3DPrinting/Robot_Mallet.STL
96.0 x 96.0 x 23.5
