Raviolifun/FiveBarRobot/CAD_Model/Linkage/MalletTube.SLDPRT

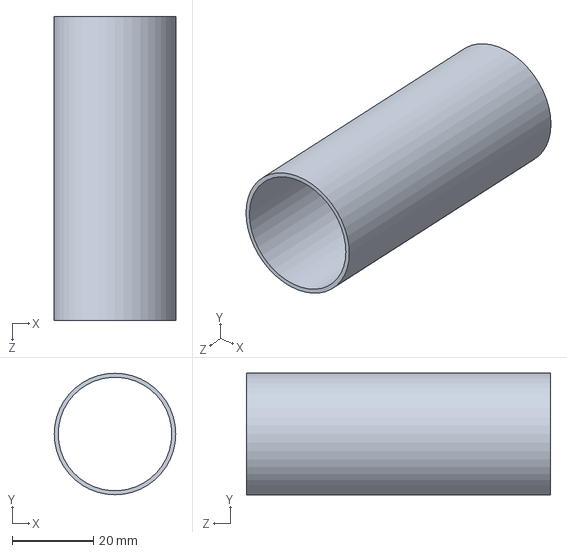
[picture p78: CAD file, 2023-04-05]
CAD_Model/Linkage/MalletTube.SLDPRT
30.0 x 30.0 x 75.0 mm
