Raviolifun/FiveBarRobot/CAD_Model/AirTable/SubParts/Side2.SLDPRT

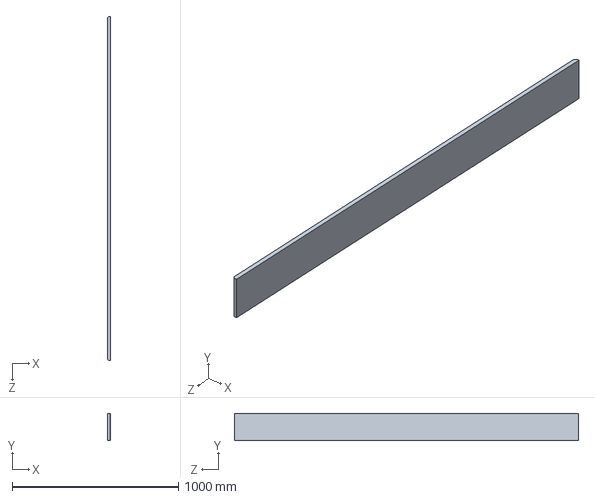
[picture p80: CAD file, 2023-02-06]
CAD_Model/AirTable/SubParts/Side2.SLDPRT
19.1 x 165.1 x 2070.1 mm
