Raviolifun/FiveBarRobot/CAD_Model/Electronics/raspberry-pi-4-model-b-1.snapshot.3/Broadcom BCM2711B0 CPU, RPi4ModelB.SLDPRT

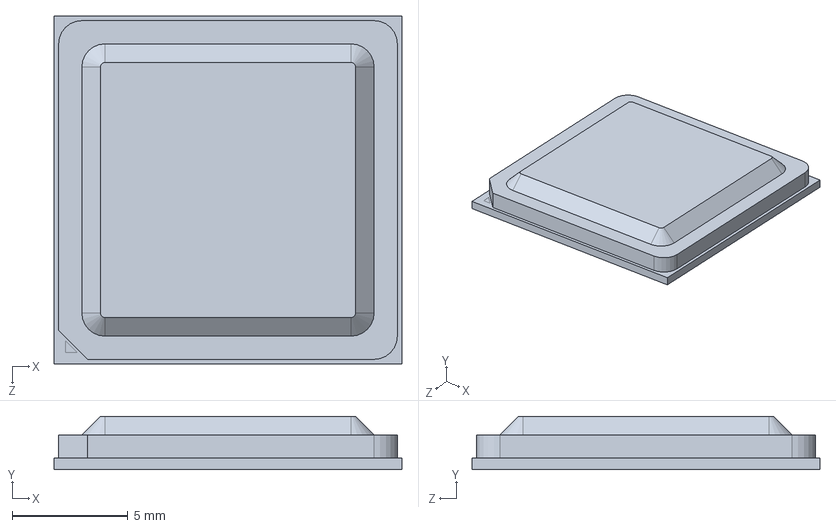
[picture p81: CAD file, 2023-01-13]
CAD_Model/Electronics/raspberry-pi-4-model-b-1.snapshot.3/Broadcom BCM2711B0 CPU, RPi4ModelB.SLDPRT
15.0 x 2.30 x 15.0 mm
