Raviolifun/FiveBarRobot/CAD_Model/Linkage/Shoulder Mount.SLDPRT

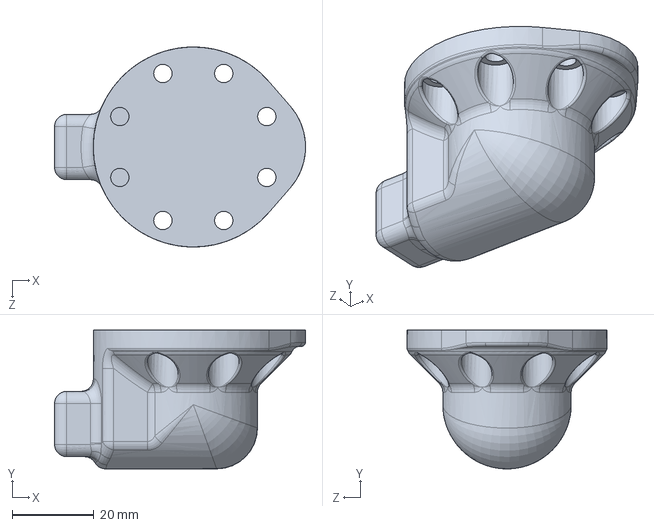
[picture p82: CAD file, 2023-04-05]
CAD_Model/Linkage/Shoulder Mount.SLDPRT
61.5 x 34.0 x 49.0 mm
