Raviolifun/FiveBarRobot/CAD_Model/Electronics/raspberry-pi-4-model-b-1.snapshot.3/Gigabit Ethernet Port, RPi4ModelB.SLDPRT

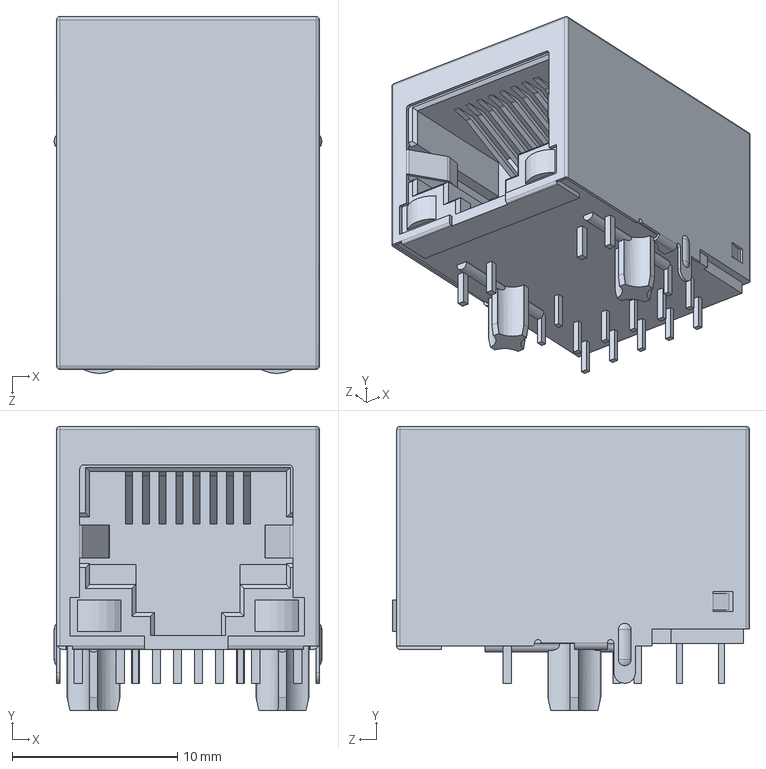
[picture p83: CAD file, 2023-01-13]
CAD_Model/Electronics/raspberry-pi-4-model-b-1.snapshot.3/Gigabit Ethernet Port, RPi4ModelB.SLDPRT
16.2 x 17.2 x 21.6 mm
