Raviolifun/FiveBarRobot/CAD_Model/Electronics/raspberry-pi-4-model-b-1.snapshot.3/PCB, RPi4ModelB.SLDPRT

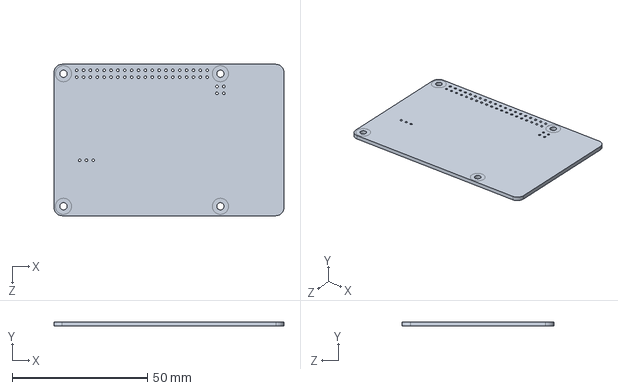
[picture p84: CAD file, 2023-01-13]
CAD_Model/Electronics/raspberry-pi-4-model-b-1.snapshot.3/PCB, RPi4ModelB.SLDPRT
85.0 x 1.60 x 56.0 mm
