Raviolifun/FiveBarRobot/CAD_Model/Linkage/Forearm.SLDPRT

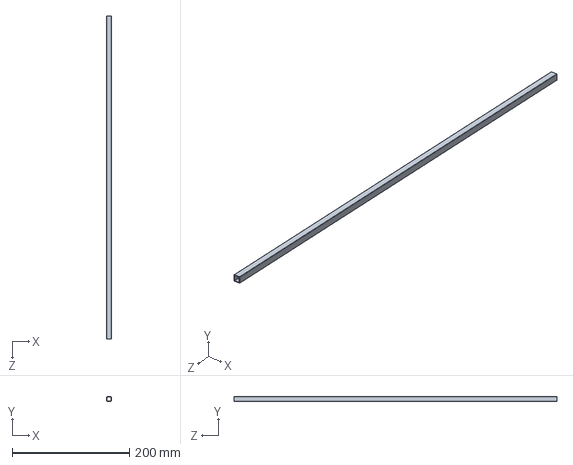
[picture p85: CAD file, 2023-02-09]
CAD_Model/Linkage/Forearm.SLDPRT
7.90 x 7.90 x 550.0 mm
