Raviolifun/FiveBarRobot/CAD_Model/Electronics/raspberry-pi-4-model-b-1.snapshot.3/MxL7704 Universal PMIC, RPi4ModelB.SLDPRT

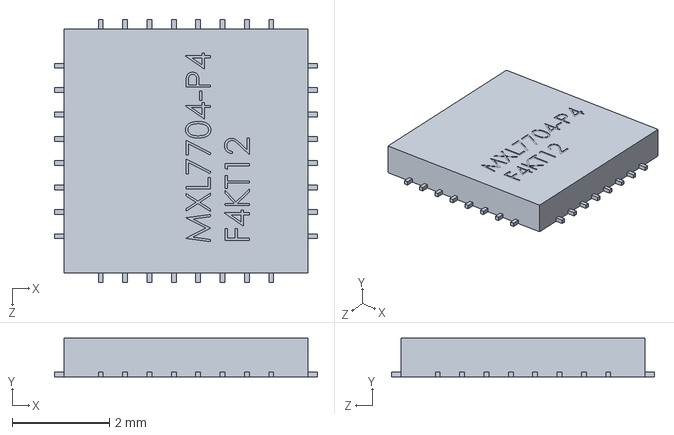
[picture p86: CAD file, 2023-01-13]
CAD_Model/Electronics/raspberry-pi-4-model-b-1.snapshot.3/MxL7704 Universal PMIC, RPi4ModelB.SLDPRT
5.40 x 0.8 x 5.40 mm
