Raviolifun/FiveBarRobot/CAD_Model/Linkage/Shoulder Arm.SLDPRT

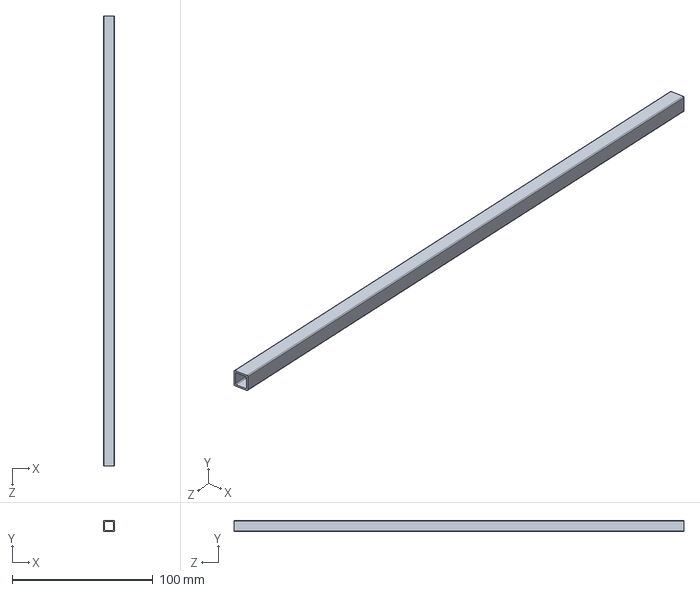
[picture p87: CAD file, 2023-02-09]
CAD_Model/Linkage/Shoulder Arm.SLDPRT
7.90 x 7.90 x 320.0 mm
