Raviolifun/FiveBarRobot/CAD_Model/Electronics/raspberry-pi-4-model-b-1.snapshot.3/Microphone Plug, RPi4ModelB.SLDPRT

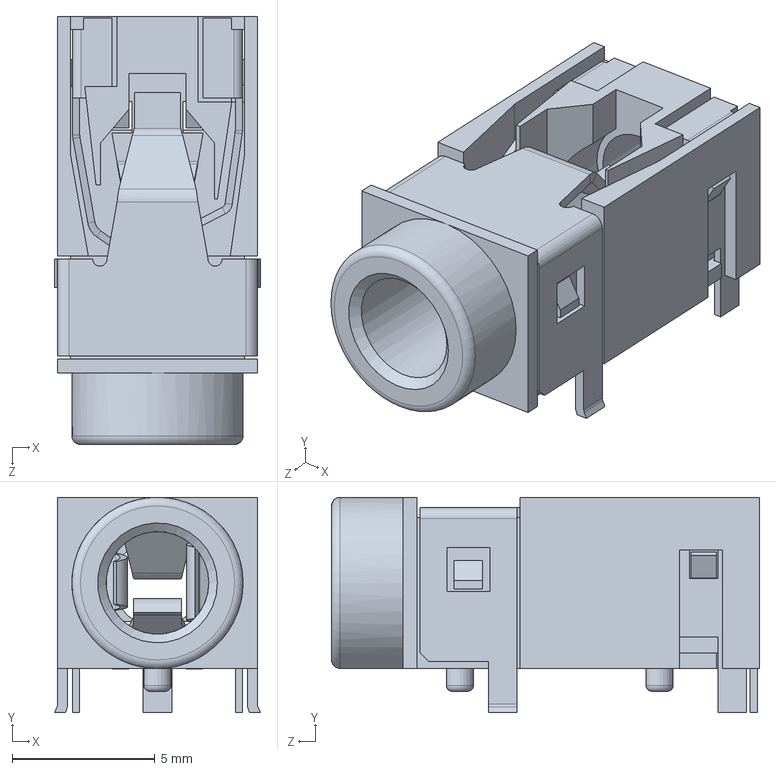
[picture p88: CAD file, 2023-01-13]
CAD_Model/Electronics/raspberry-pi-4-model-b-1.snapshot.3/Microphone Plug, RPi4ModelB.SLDPRT
7.23 x 7.55 x 15.0 mm
