Raviolifun/FiveBarRobot/CAD_Model/Linkage/Elbow2.SLDPRT

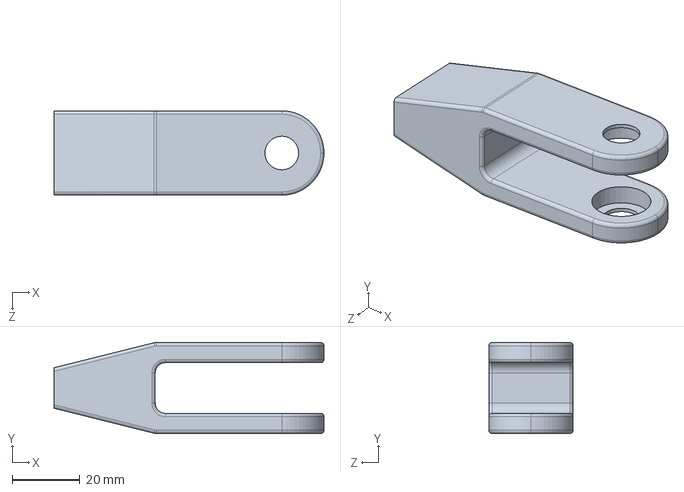
[picture p89: CAD file, 2023-02-06]
CAD_Model/Linkage/Elbow2.SLDPRT
80.0 x 27.0 x 25.0 mm
