Raviolifun/FiveBarRobot/CAD_Model/Electronics/raspberry-pi-4-model-b-1.snapshot.3/2X USB2.0 PORTS, RPi4ModelB.SLDPRT

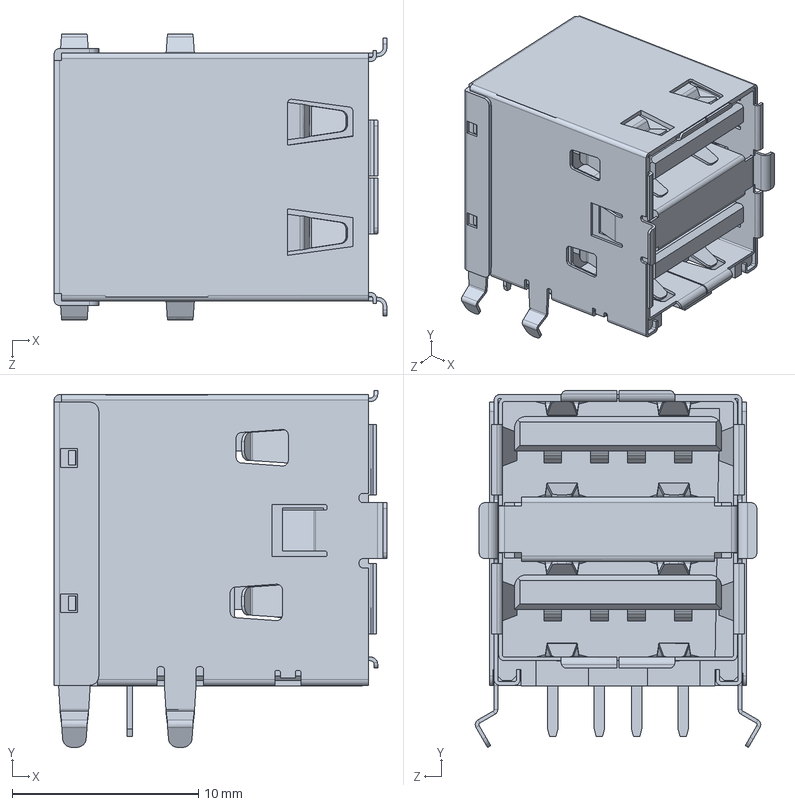
[picture p90: CAD file, 2023-01-13]
CAD_Model/Electronics/raspberry-pi-4-model-b-1.snapshot.3/2X USB2.0 PORTS, RPi4ModelB.SLDPRT
17.9 x 19.2 x 15.3 mm
