Raviolifun/FiveBarRobot/CAD_Model/Linkage/Elbow1.SLDPRT

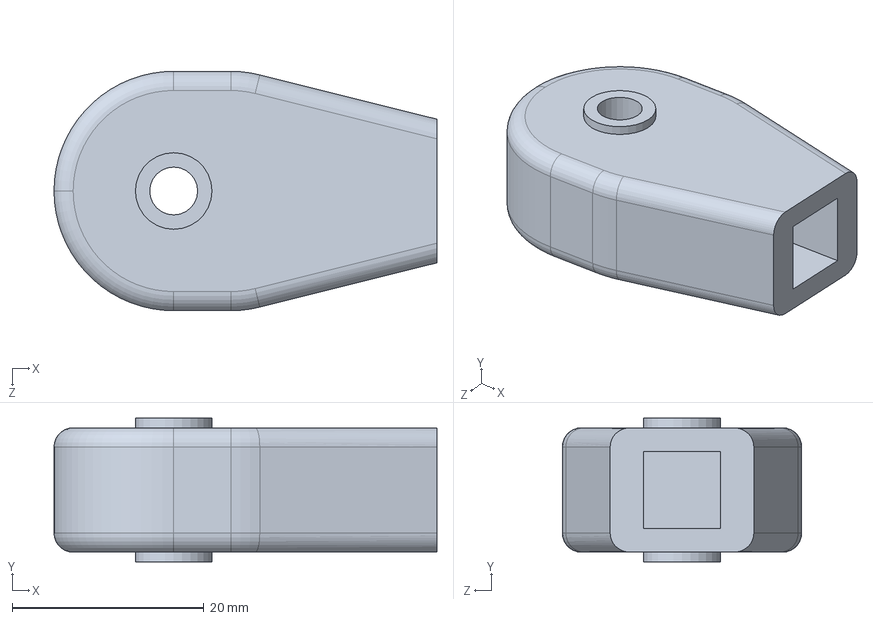
[picture p92: CAD file, 2023-02-06]
CAD_Model/Linkage/Elbow1.SLDPRT
40.0 x 15.0 x 25.0 mm
