Raviolifun/FiveBarRobot/CAD_Model/Linkage/EndJoint.SLDPRT

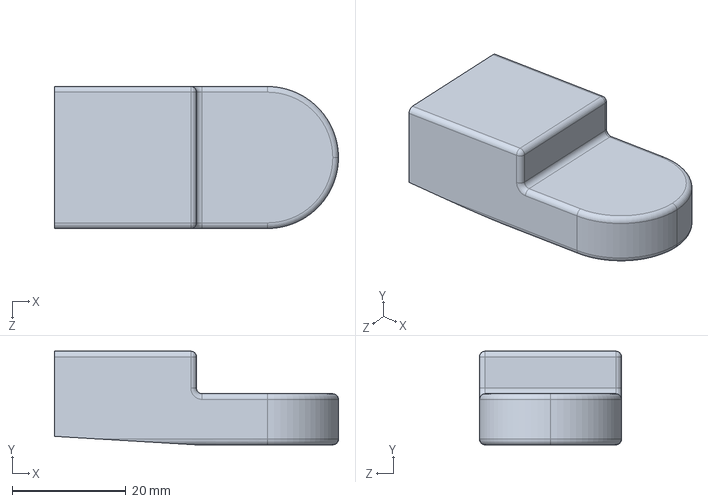
[picture p93: CAD file, 2023-01-26]
CAD_Model/Linkage/EndJoint.SLDPRT
50.0 x 16.5 x 25.0 mm
