Raviolifun/FiveBarRobot/CAD_Model/Electronics/raspberry-pi-4-model-b-1.snapshot.3/SD Card Slot, RPi4ModelB.SLDPRT

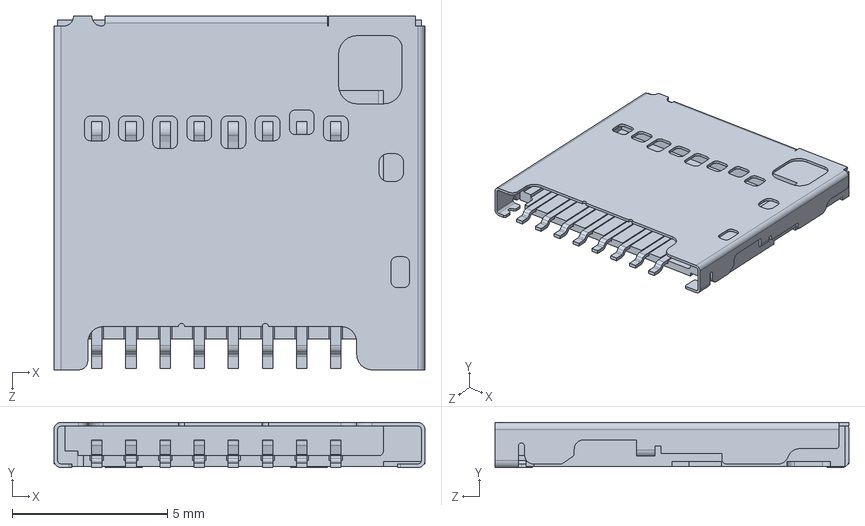
[picture p94: CAD file, 2023-01-13]
CAD_Model/Electronics/raspberry-pi-4-model-b-1.snapshot.3/SD Card Slot, RPi4ModelB.SLDPRT
11.9 x 1.45 x 11.4 mm
