Raviolifun/FiveBarRobot/Saves/animation_test.gif

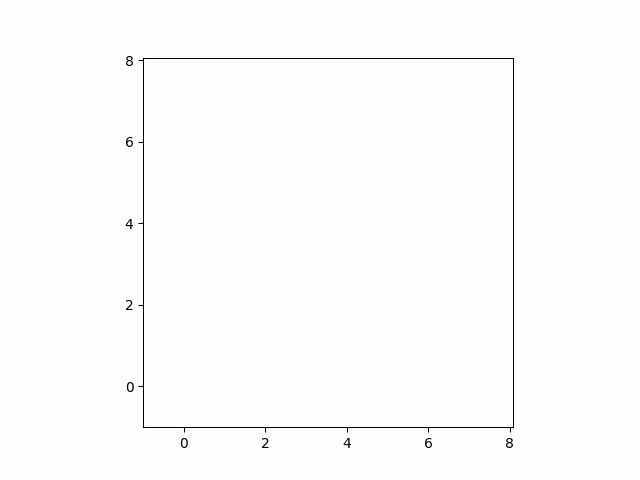
Saves/animation_test.gif
